sheilsarda/IoT_Thermal_Camera/Lab2/Nikhil Jamdade_A0.pdf

A0 Assignment – ESE516-SPRING 2019 Nikhil Jamdade

Device Description

In developing countries, the patient monitoring systems used in hospitals are not holistically designed compare to the type of monitoring necessary for the patient’s healthcare. The monitoring systems are manual and thus requires time to time check-ups. With increasing number of patients and less availability of resources, hospitals are facing a problem in efficient monitoring system. It is difficult to monitor patient’s health patterns and analyze them. The quality of sleep can be an early indicator of dementia and serious health conditions including adverse reactions to medications, depression and stress. Moreover, some of the vital parameters are really important for early diagnosis of certain medical conditions and understand health status.

The designed IOT device “SmartEye” monitors patient’s sleep, resting pattern, body thermal map and body temperature in real time, in a non-contact way without any wires and devices attached to patients’ body. The system provides patient’s real time temperature, video analysis and thermal analysis. The information from the SmartEye can be accessed and analyzed from the monitoring room or on mobile device application. The ability to track patient’s movement and position non-invasively and monitor them remotely with mobile or desktop applications makes great sense to improve both safety and vigilance. The data received from the product can be analyzed for proper treatment of patient and hospital logistics.

The IOT product SmartEye uses electronic sensors like IR sensor, visible and IR camera module, processing and wireless transmission unit and computational imaging techniques. The patient’s data are acquired using sensor modules and processed using microcontroller (SAMD21). The data is transmitted using WIFI Chip (WINC1500) and internet to personal device or user interface. Though thermal imaging and image analysis is not in widely in practice in medical field before because of only recent development of thermal imaging devices techniques. There is huge scope medical diagnosis by analyzing thermal images and data mining.

Basic Interaction interface of SmartEye

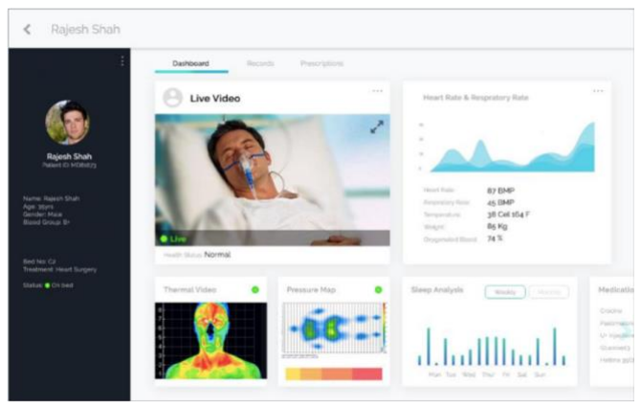
[picture p23: figure]

Simple System Diagram

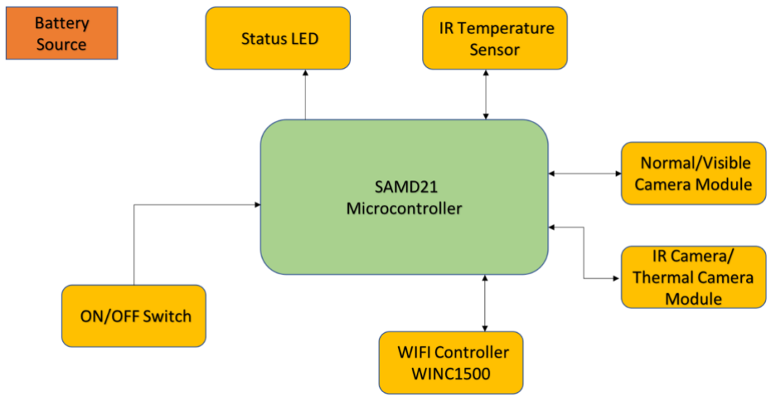
[picture p24: figure]

Device Investigation and Bill of Materials

The excel file having bill of material with its description and links to datasheets is attached with submission.

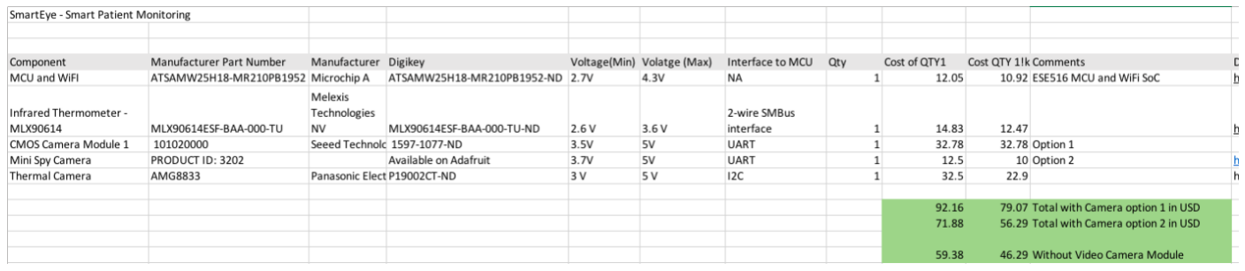
[picture p25: figure]
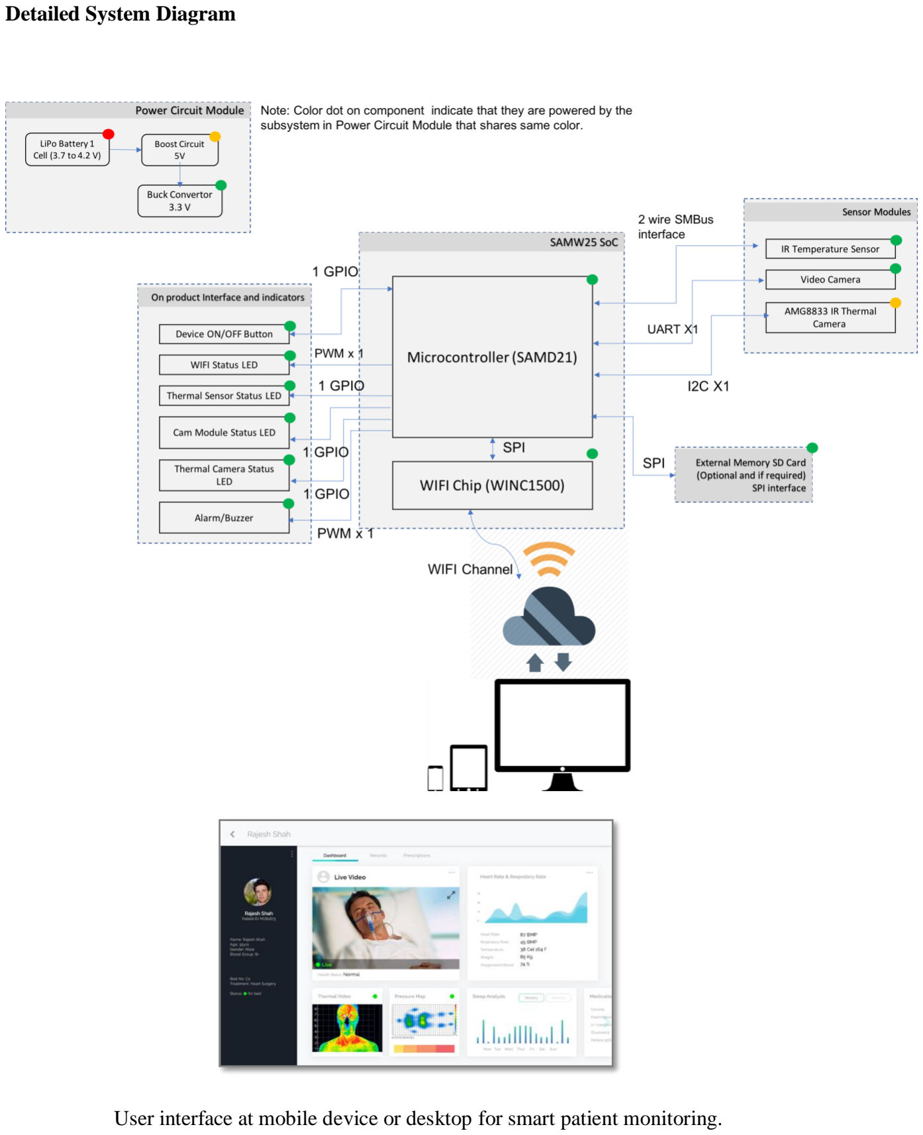
[picture p26: page 3]

Detailed System Diagram

User interface at mobile device or desktop for smart patient monitoring.
