sheilsarda/IoT_Thermal_Camera/Slides/Final_Proj.pdf

# Radiance T

## IOT for Non Contact Temperature Measurement and Thermal Image Mapping

Nikhil Jamdade | Sheil Sarda
Mentor: Eduardo Garcia
ESE 516 IOT Edge Computing | 1st May 2019 | Slide 1/4

## Radiance T – IOT edge Computing

Major Applications -
- Industry 4.0
- Assembly and Manufacturing line
- Smart Retail and Supply Chain
- Consumer and Product Analytics

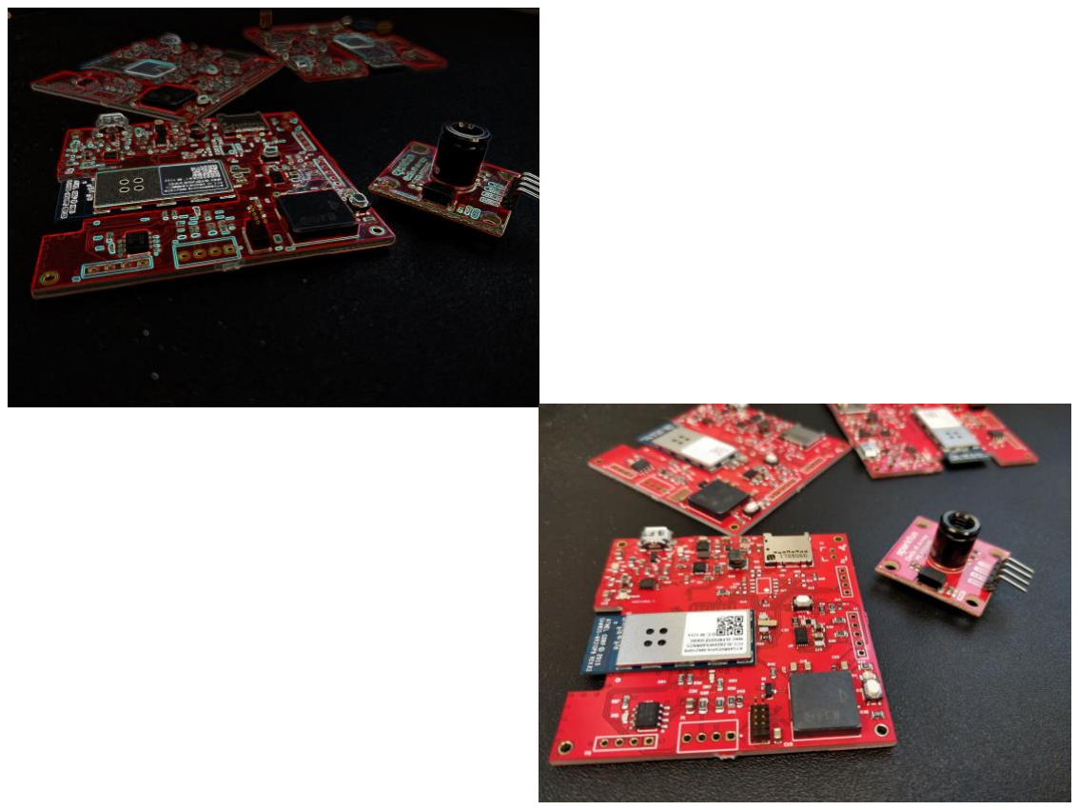
[picture p28: figure]

Device –
1. SAMD 25 WINC 1500
2. IR Sensor and Thermal Camera
3. Fuel Gauge
4. Real Time Update on Cloud Service
5. Analytics Interface

## Roadmap and Challenges

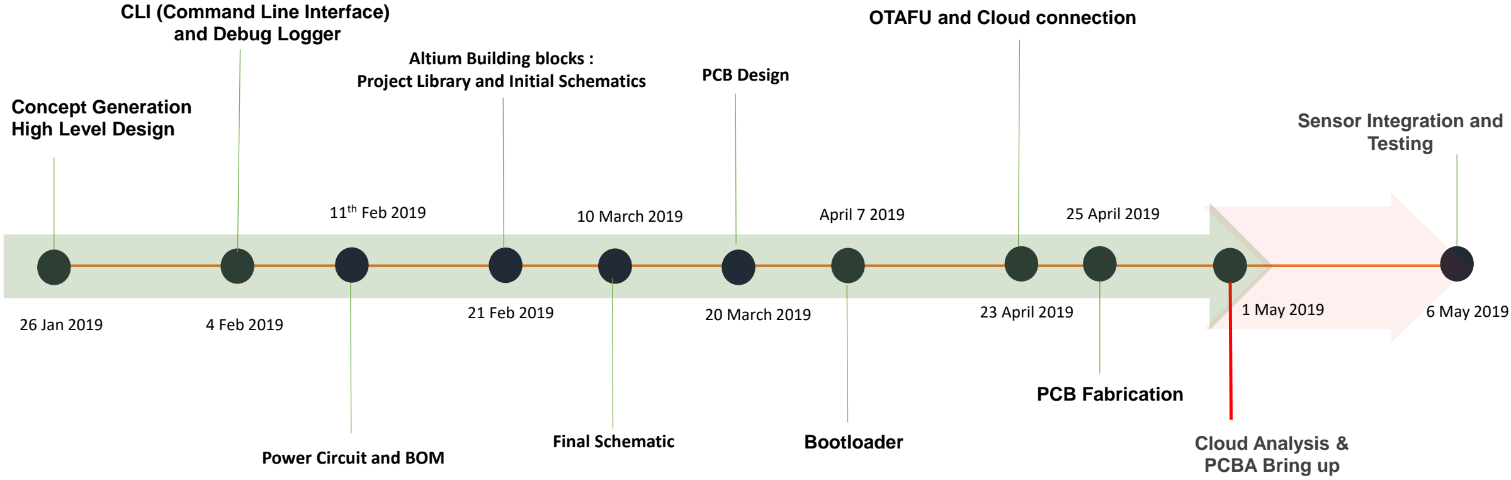
[picture p29: figure]
Concept Generation High Level Design; CLI (Command Line Interface) and Debug Logger; PCB Fabrication; OTAFU and Cloud connection; 26 Jan 2019; 4 Feb 2019; 21 Feb 2019; 20 March 2019; 23 April 2019; Bootloader; Cloud Analysis &; PCBA Bring up; Sensor Integration and Testing; Power Circuit and BOM; Altium Building blocks :; Project Library and Initial Schematics; PCB Design; 25 April 2019; 1 May 2019; 6 May 2019; April 7 2019 th Feb 2019; Final Schematic; 10 March 2019

## Interacting with Radiance T

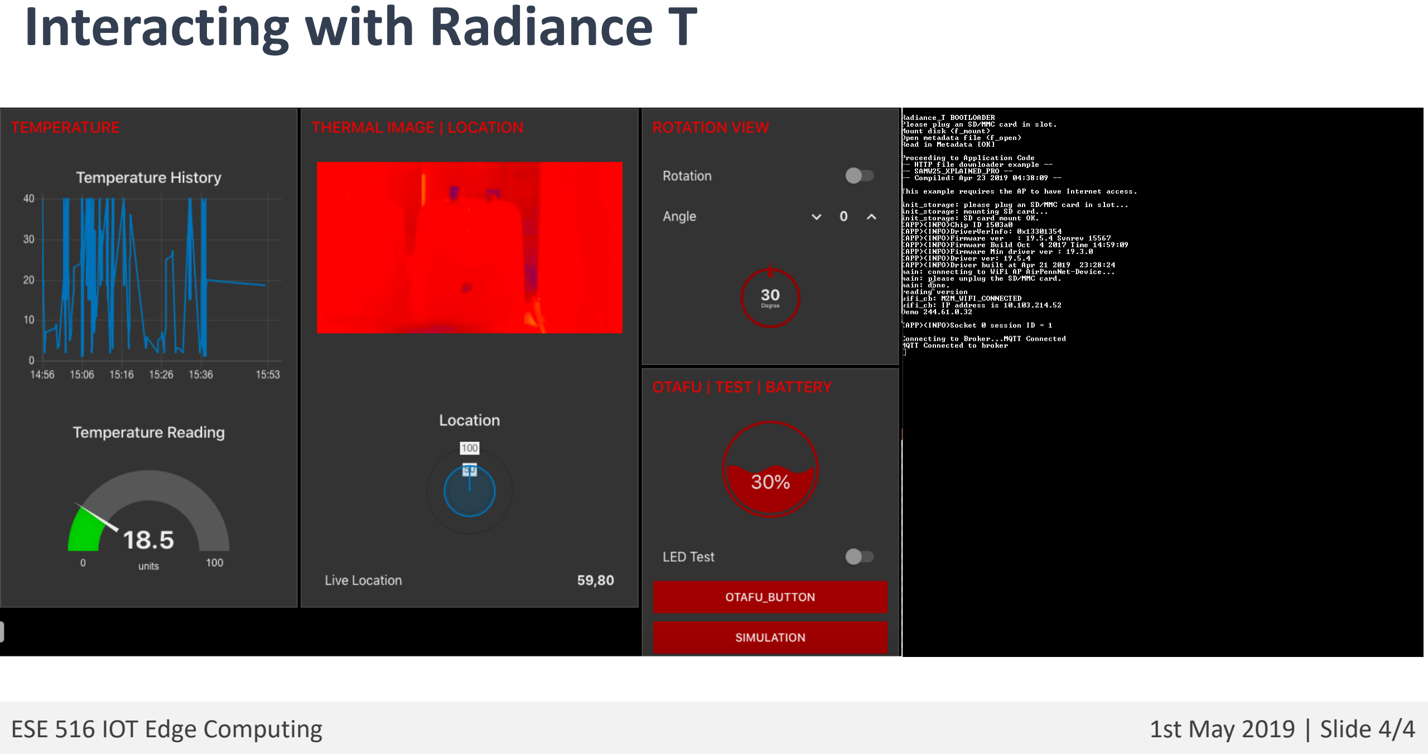
[picture p30: page 4]
