sheilsarda/IoT_Thermal_Camera/Lab7/A7 Submission/Q1_Node_Red/Flow Diagram.pdf

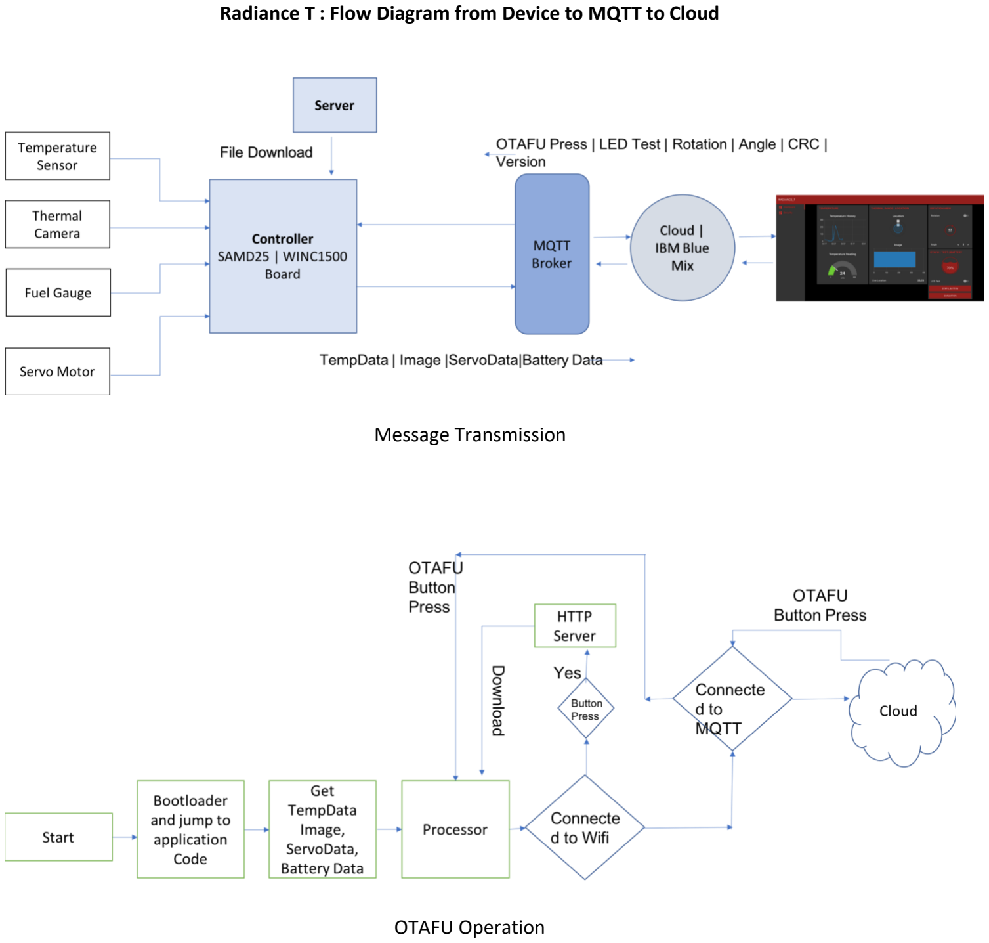
[picture p136: page 1]

Radiance T : Flow Diagram from Device to MQTT to Cloud

Message Transmission

OTAFU Operation

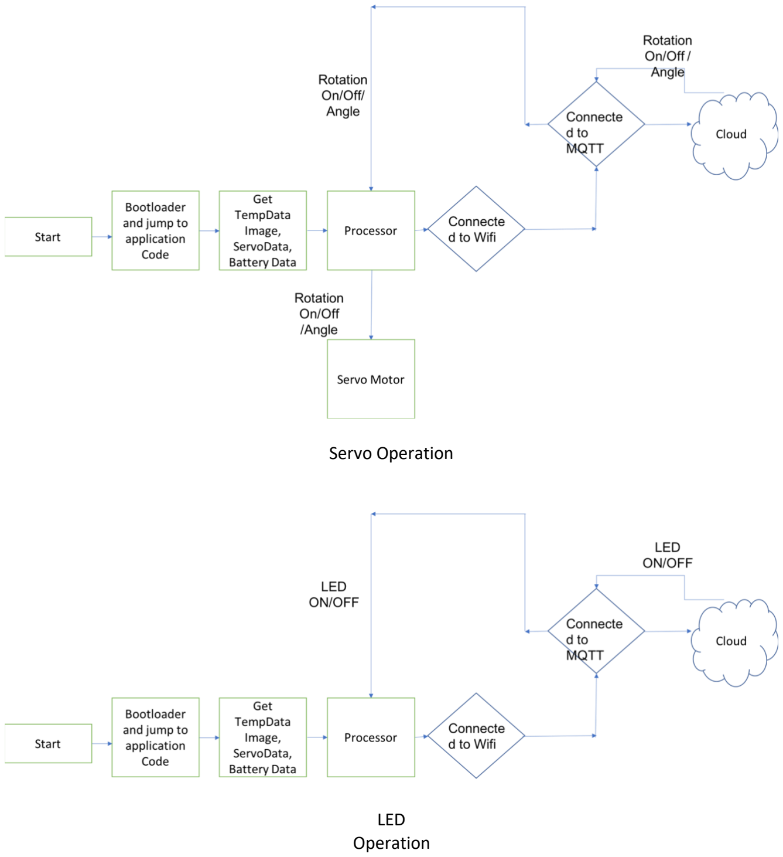
[picture p137: page 2]

Servo Operation

LED
Operation

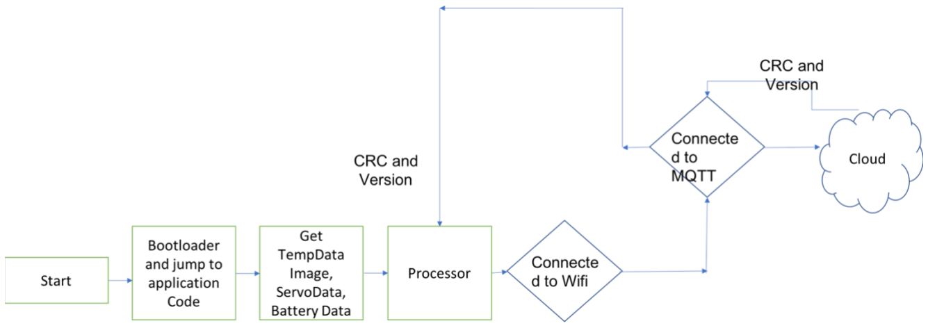
[picture p138: figure]

MetaData Trasfer
