sheilsarda/IoT_Thermal_Camera/Lab7/A7 Submission/Q1_Node_Red/Radiance T_Node Red Simulator .pdf

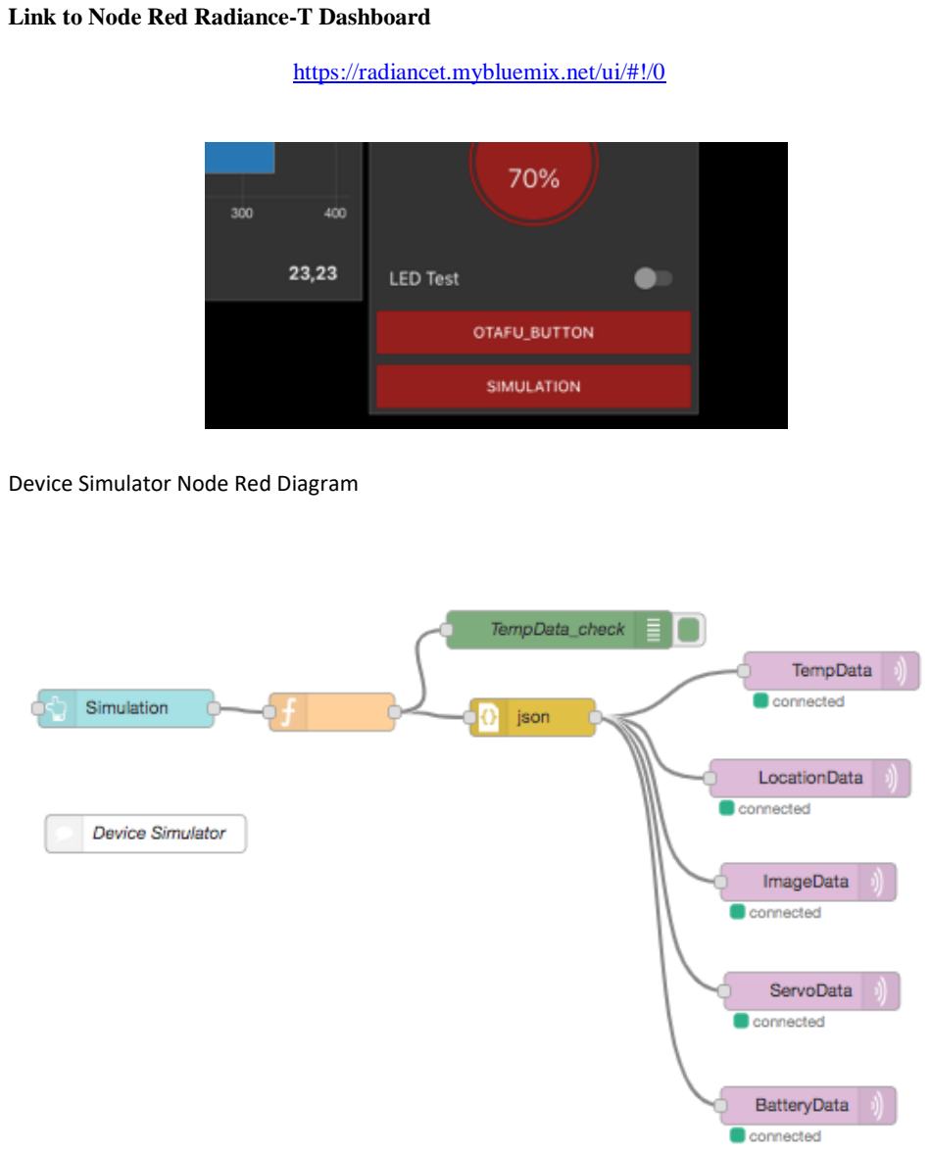
[picture p139: page 1]

Link to Node Red Radiance-T Dashboard

https://radiancet.mybluemix.net/ui/#!/0

Device Simulator Node Red Diagram
