sheilsarda/IoT_Thermal_Camera/Lab1/ESE516 A1.pdf

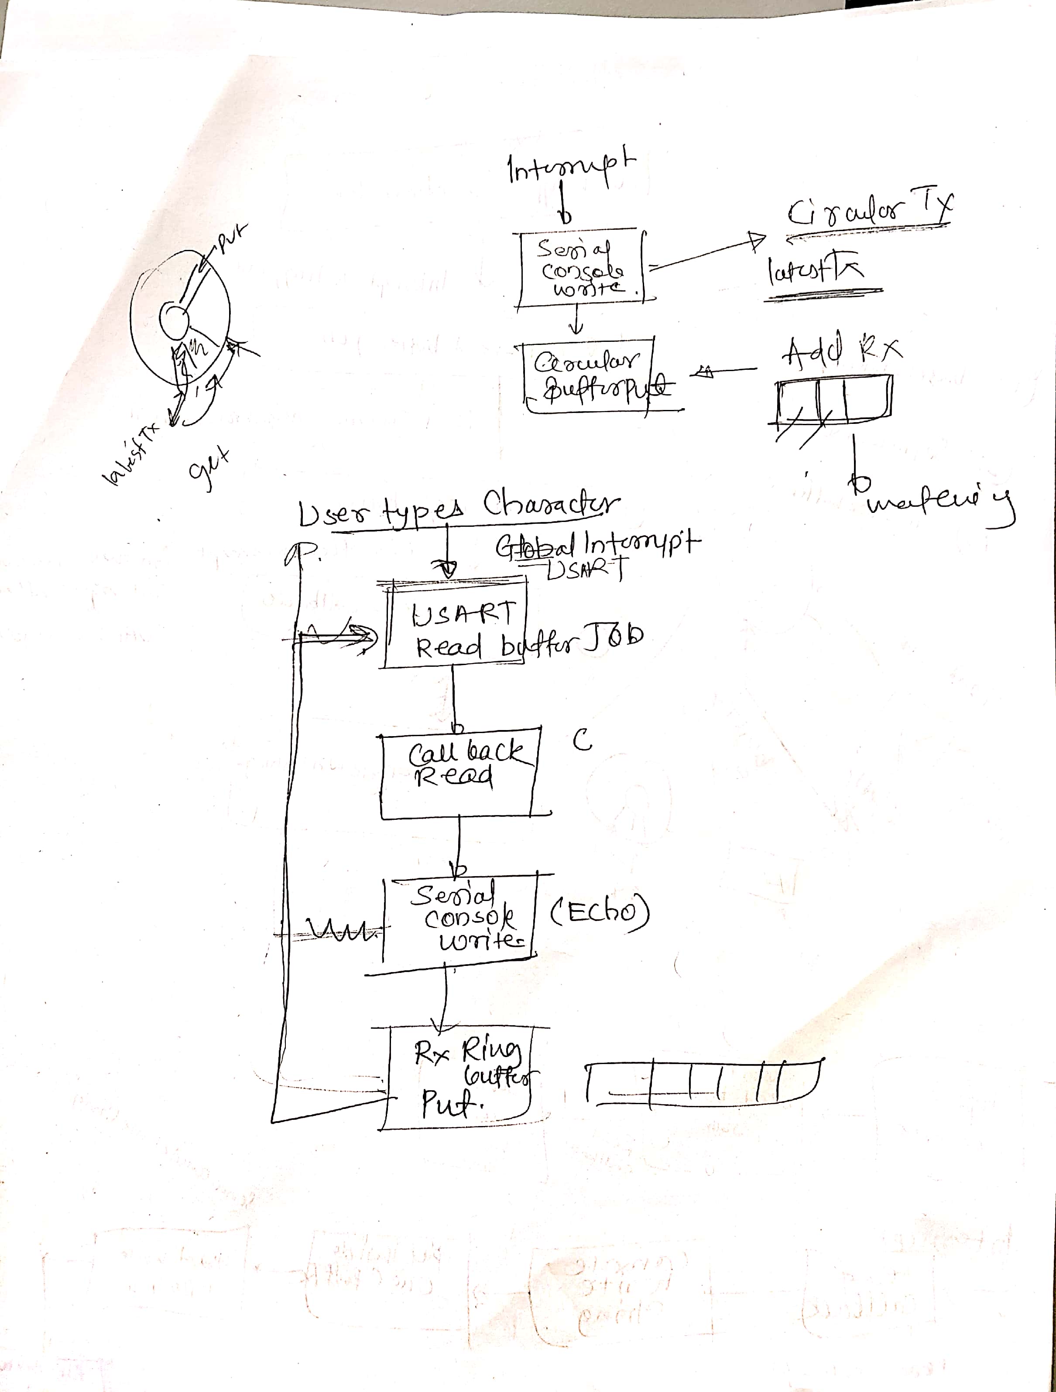
[picture p149: page 1]

Scanned by CamScanner

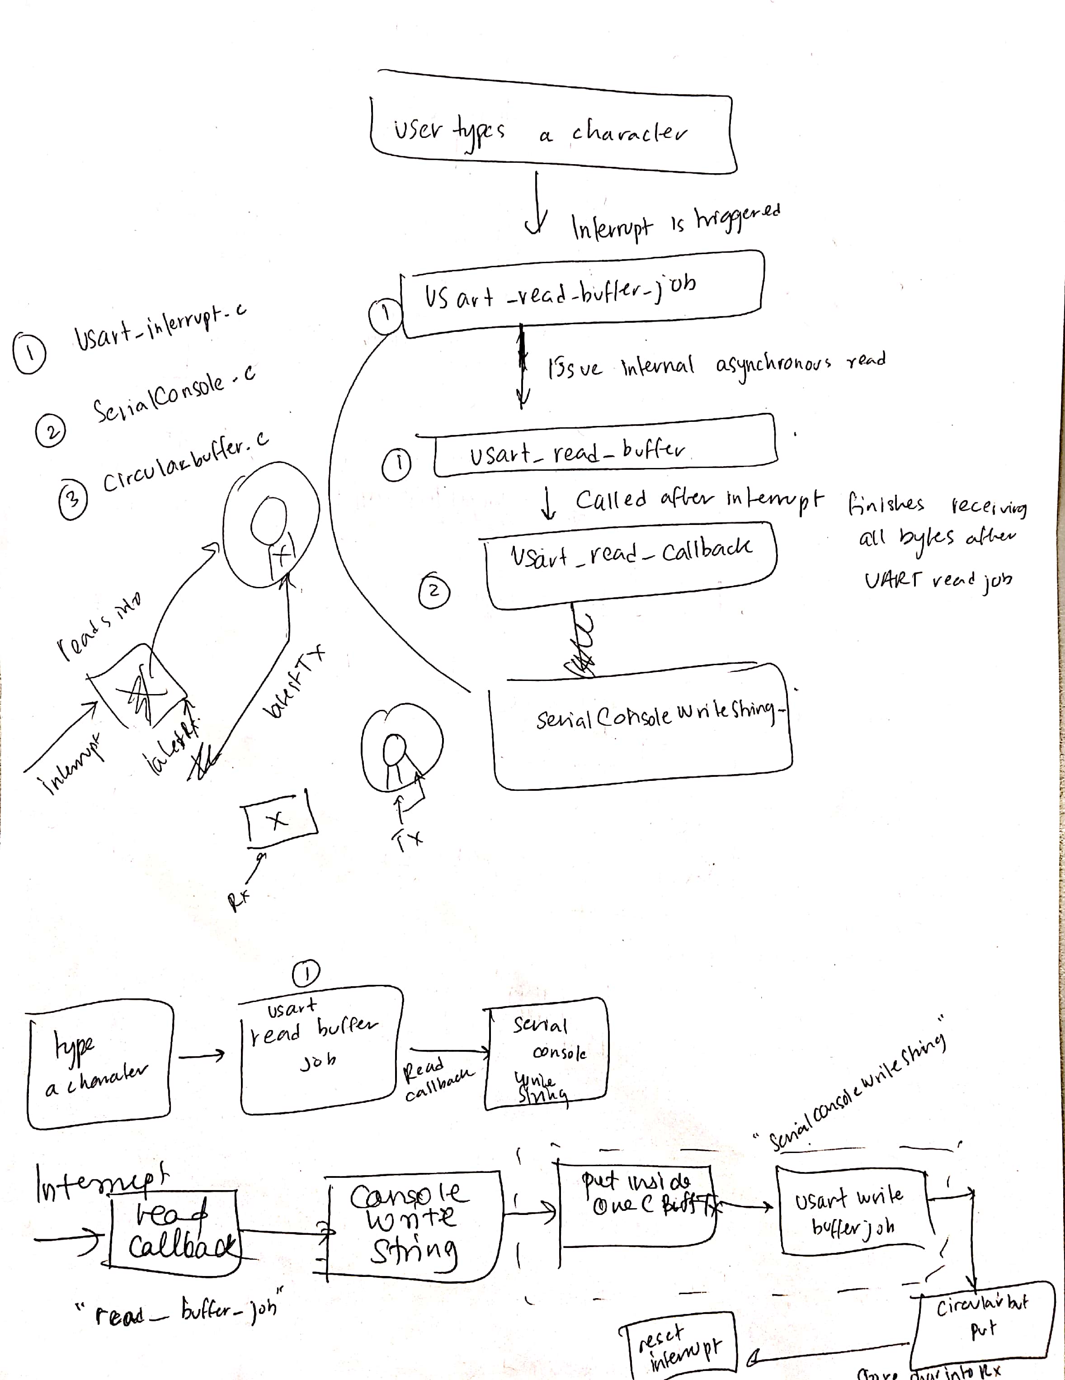
[picture p150: page 2]
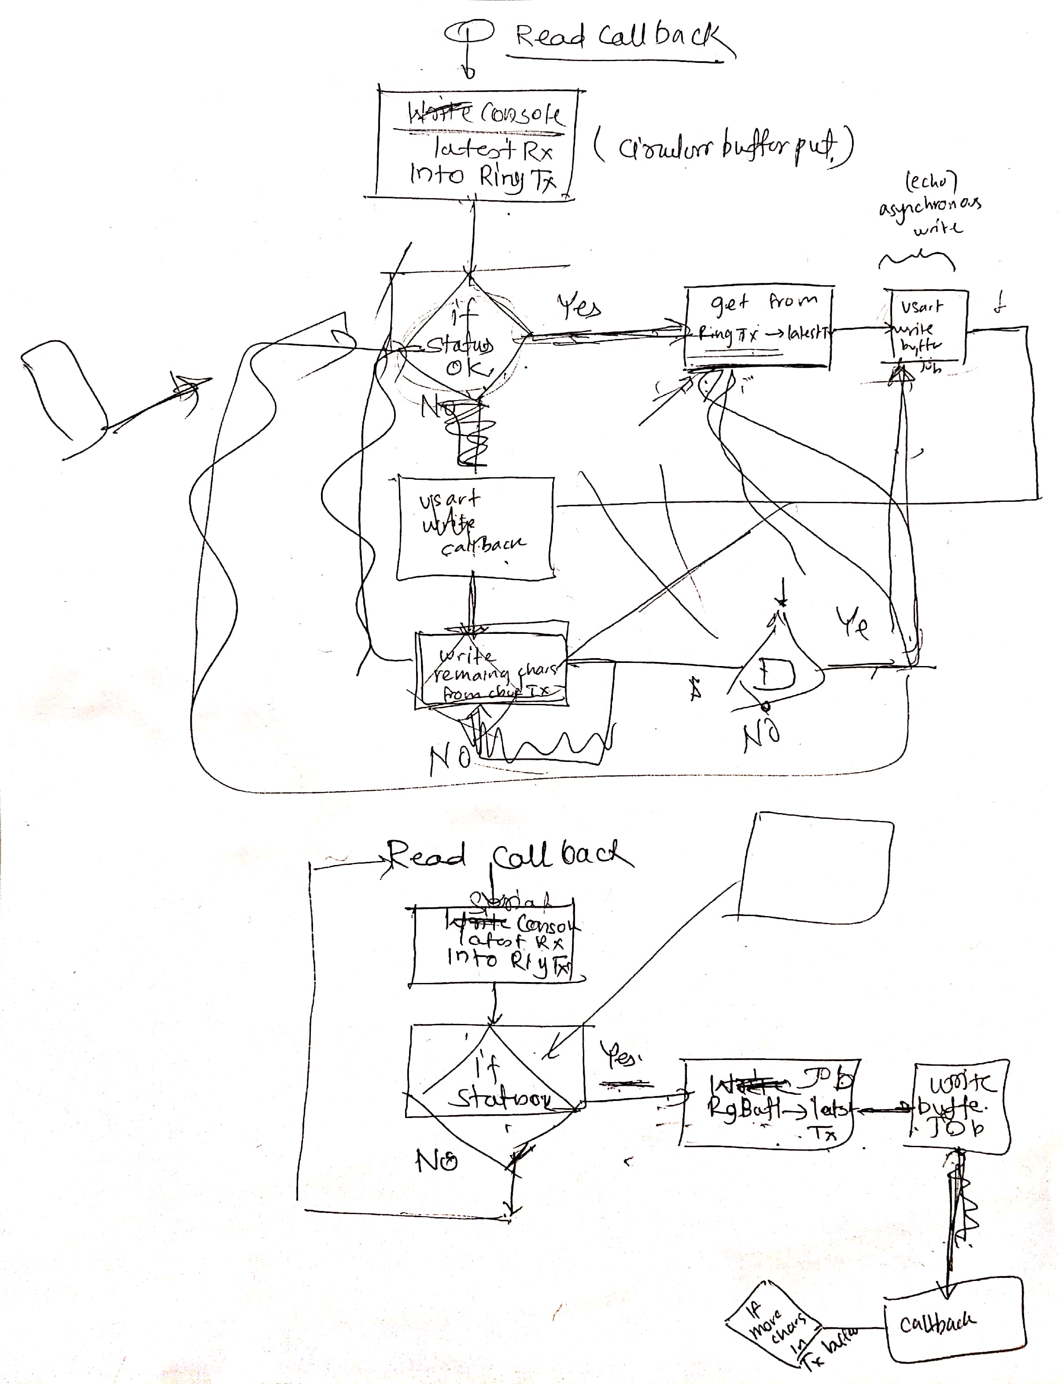
[picture p151: page 3]
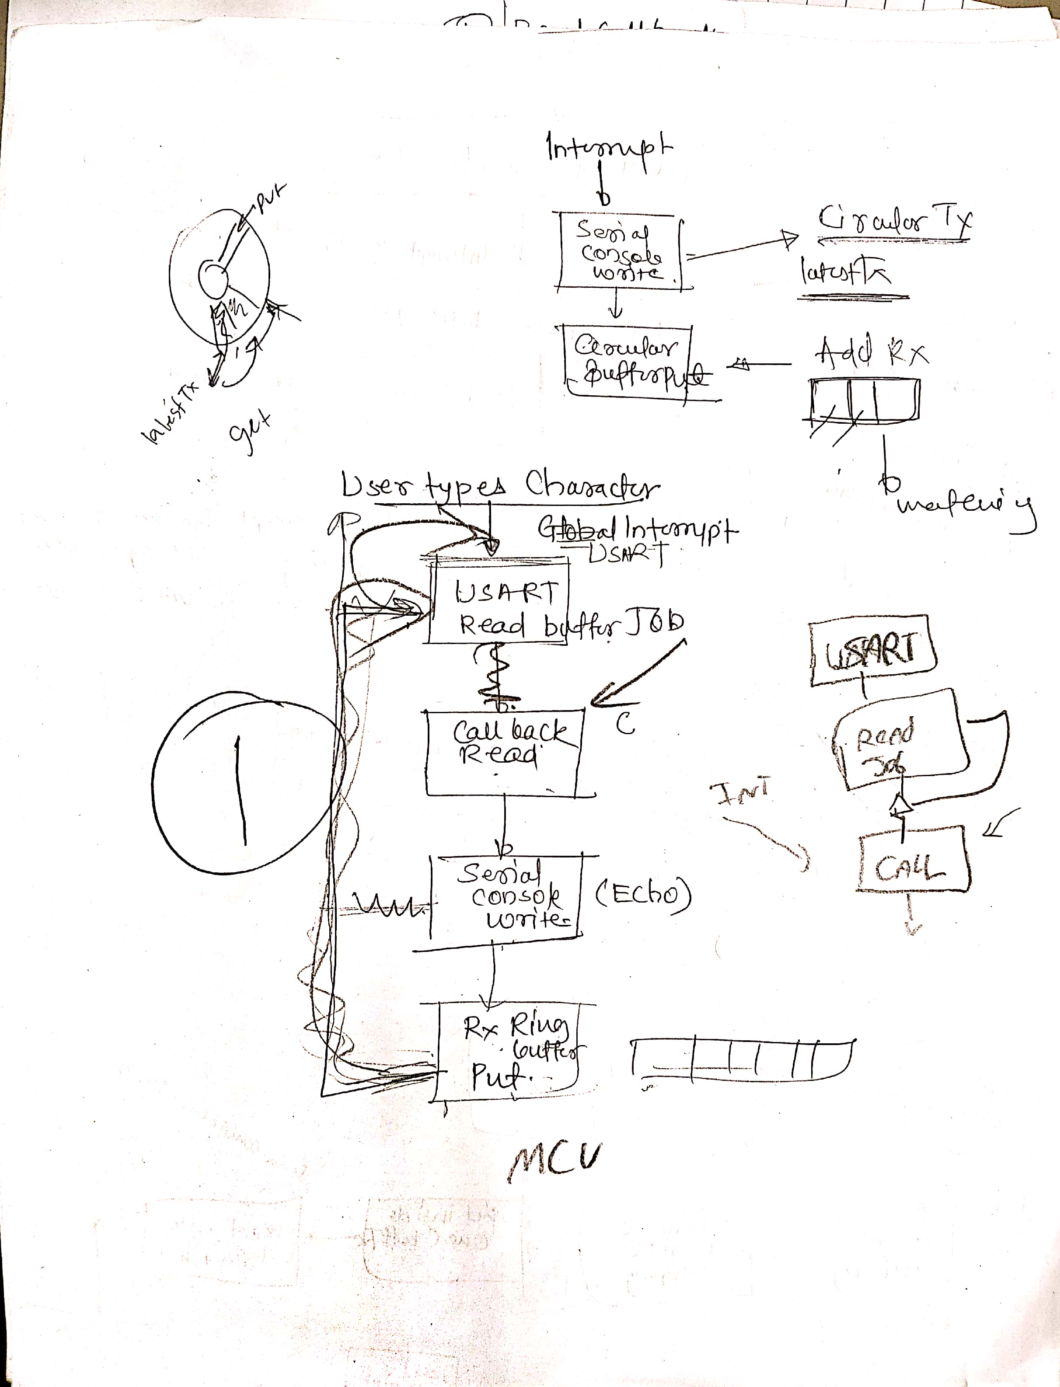
[picture p152: page 4]
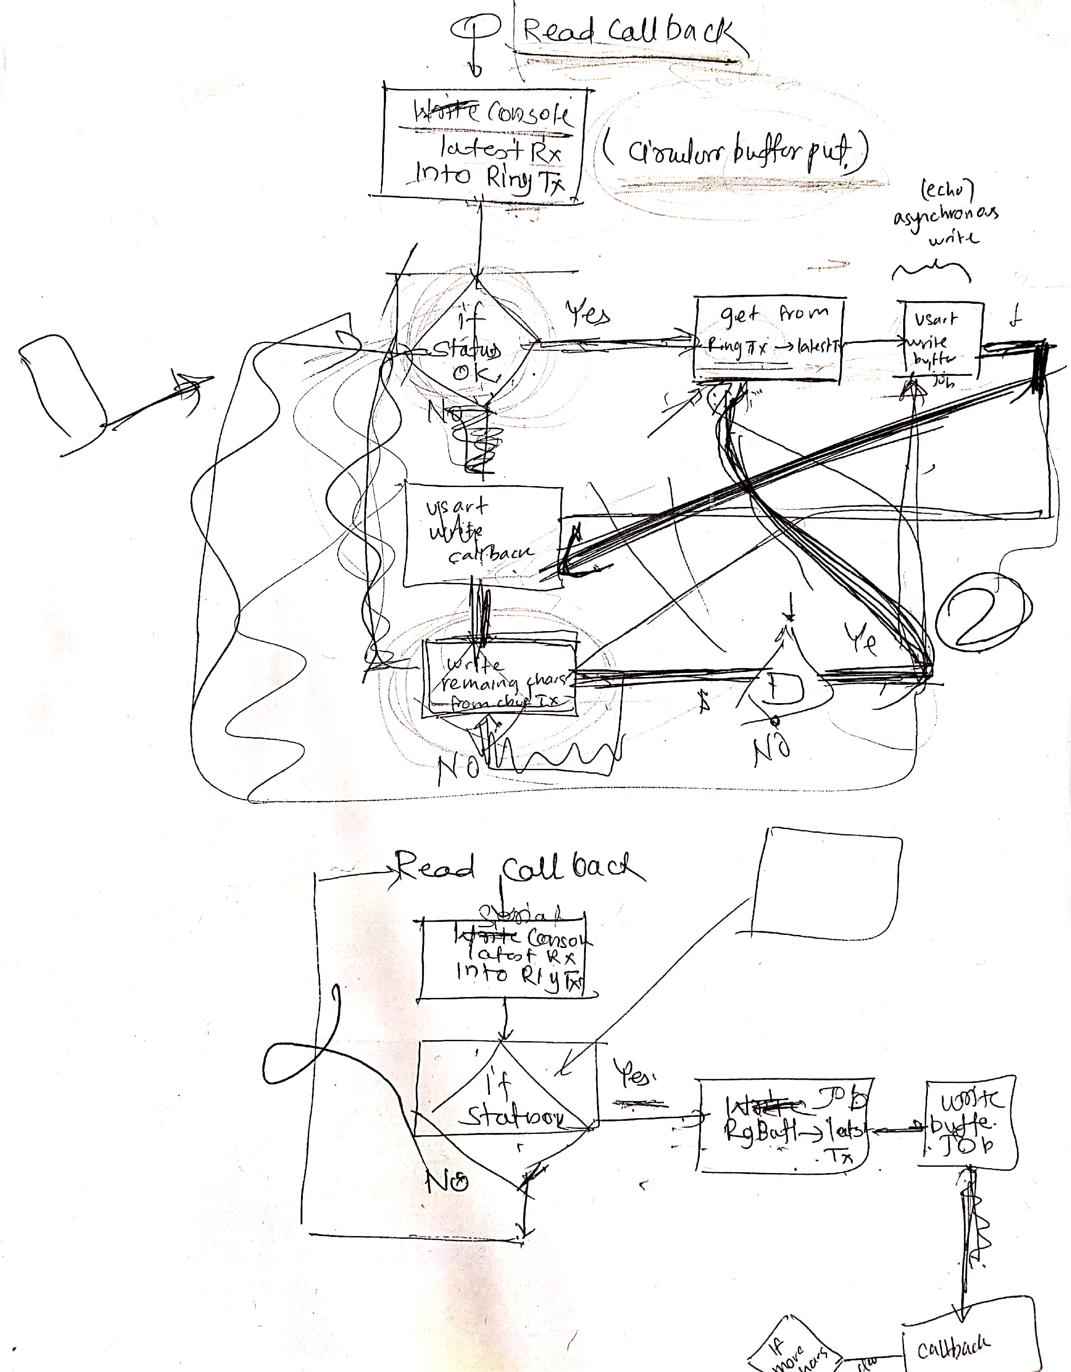
[picture p153: page 5]
