sheilsarda/IoT_Thermal_Camera/Slides/Lecture16_ESE516_2019-1.pdf

# L16: FLASH LAB

ESE516: IoT Edge Computing Wednesday March 28 2019
Eduardo Garcia – edgarc@seas.upenn.edu

## RASPBERRY PI(DAY) ZERO W ANTENNA

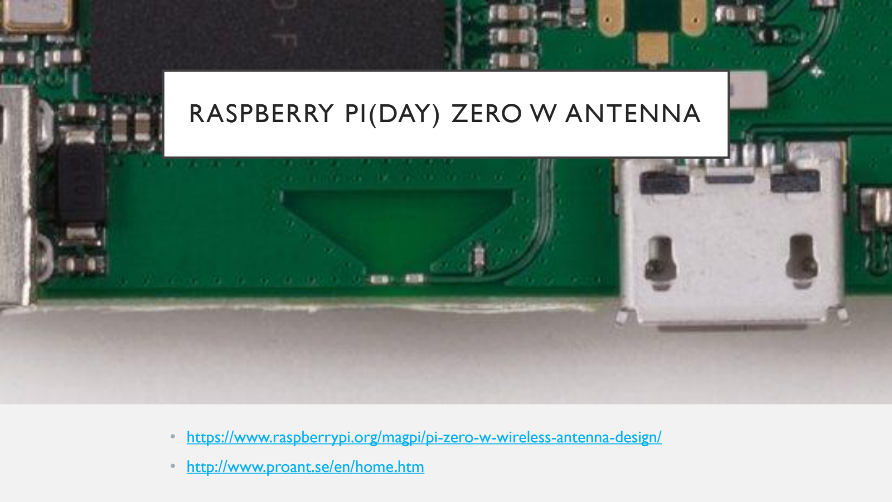
[picture p154: page 2]

- https://www.raspberrypi.org/magpi/pi-zero-w-wireless-antenna-design/
- http://www.proant.se/en/home.htm

## TODAY’S LAB GOALS

1. Atmel Studio Solution
1. Create 2-project solution, including bootloader + app code
2. Modify the linker and program erasure settings
2. Flash
1. Connect to your Flash IC using the ASF driver.
2. Read in the Flash ID to validate the connection.
3. Read a memory location in flash.
4. Erase a memory location in flash.
5. Write a memory location in flash.

## BONUS GOALS

If you happen to get through all of the flash…

1. Import and test the ASF CRC32 driver.
1. Try running the checksums on a bunch of generated data, writing it to flash, reading it back out, and validating it.
2. http://asf.atmel.com/docs/3.34.1/samd21/html/group__common__services__crc32.html
2. Import and test the ASF NVM driver.
1. This writes to the SAM D21 non volatile memory. It’s what we’re going to use to write the application code to memory, while in the bootloader.
2. http://asf.atmel.com/docs/3.34.1/samd21/html/group__asfdoc__sam0__nvm__group.html

# BOOTLOADER REVIEW

## PARTITION TABLES

- Remember the caveats of your flash memory!
- How small of a chunk of memory can you erase?
- How many bytes can you write at a time?
- You must erase before writing to a section of memory.
- What do you want to store in your status page?

External
Flash
SD CARD
FILE 1 | BinaryUpdate
FILE2 | BINARY metadata
FILE 3 | Other Data
SAMD21 256kB | 0x00000 | Bootloader
| 0x01F00 | Boot status
| 0x02000 | Application Code
| 0x40000 | End of memory

## STATUS STRUCTURE

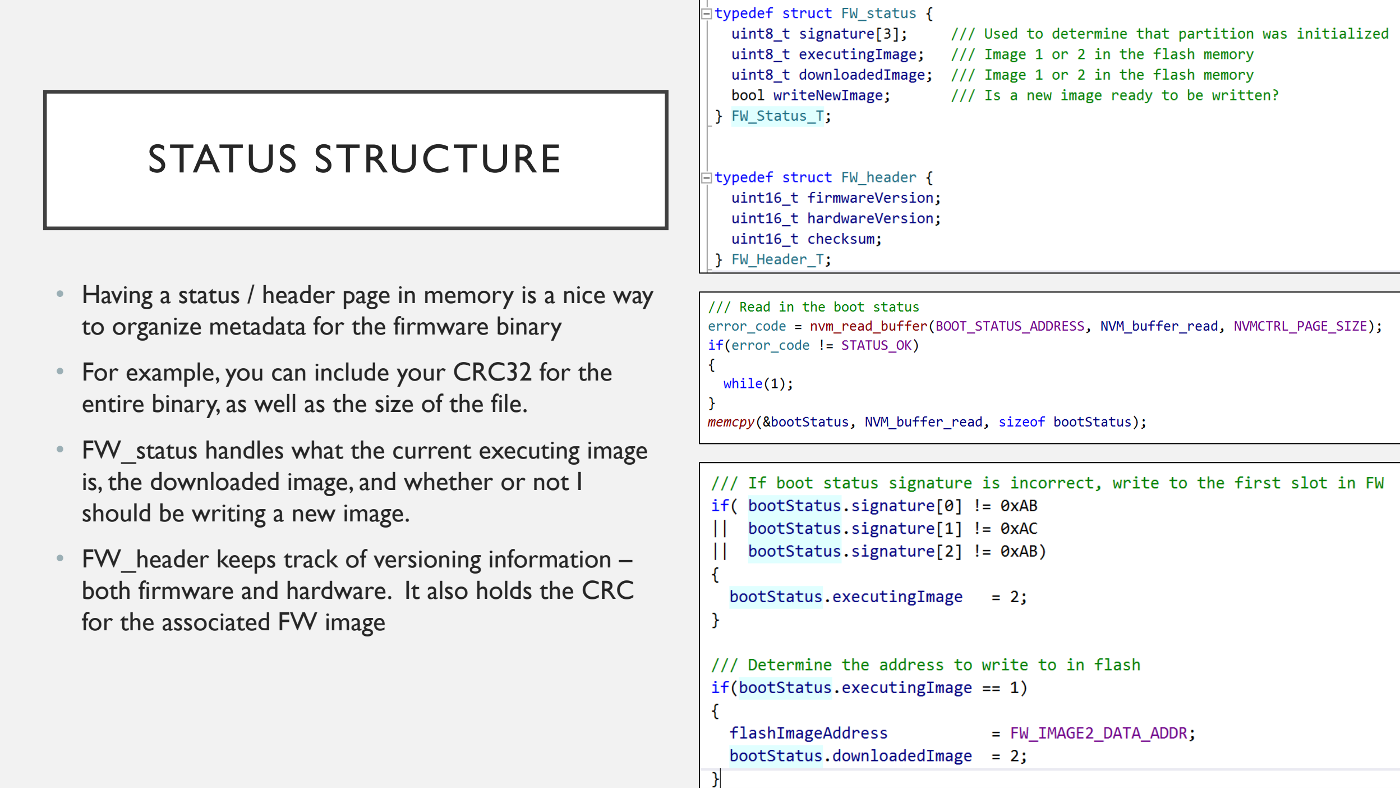
[picture p155: page 9]

- Having a status / header page in memory is a nice way to organize metadata for the firmware binary
- For example, you can include your CRC32 for the entire binary, as well as the size of the file.
- FW_status handles what the current executing image is, the downloaded image, and whether or not I should be writing a new image.
- FW_header keeps track of versioning information – both firmware and hardware. It also holds the CRC for the associated FW image

## RUNNING APPLICATION CODE

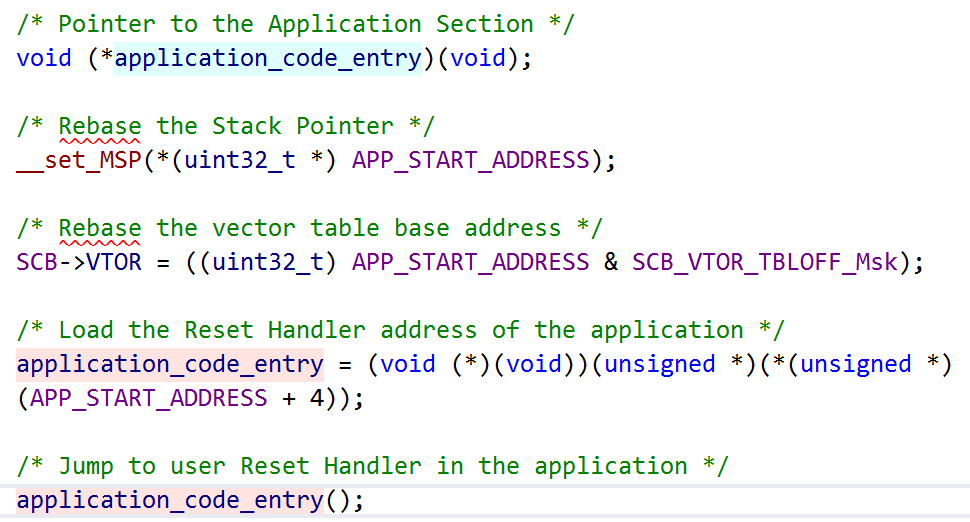
[picture p156: figure]

- On boot, the MCU will look to the 0x0000 address – this gives the stack pointer and reset handler for the bootloader
- To transition to the application code, we must point to the application code space – “rebase” the stack pointer & reset vector
- The code on the right handles this functionality
- USB MSC: Page 31-32 has some good references
- http://www.atmel.com/images/atmel-42352-sam-d21-xpro-usb-host-msc-bootloader_trainingmanual_an8185.pdf (http://www.atmel.com/images/atmel-42352-sam-d21-xpro-usb-host-msc-bootloader_training-manual_an8185.pdf)

# ATMEL STUDIO SOLUTION

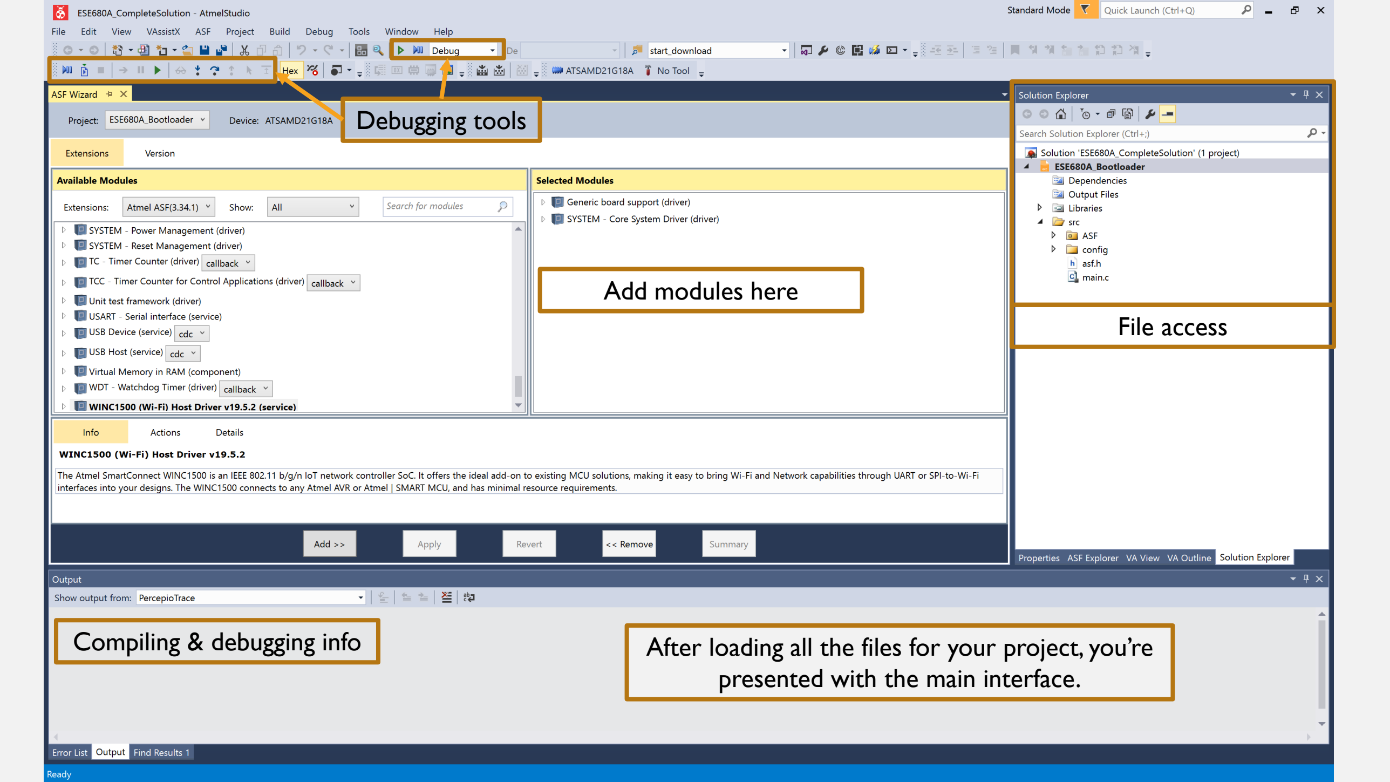
[picture p157: page 12]

File access

Compiling & debugging info

Add modules here

Debugging tools

After loading all the files for your project, you’re presented with the main interface.

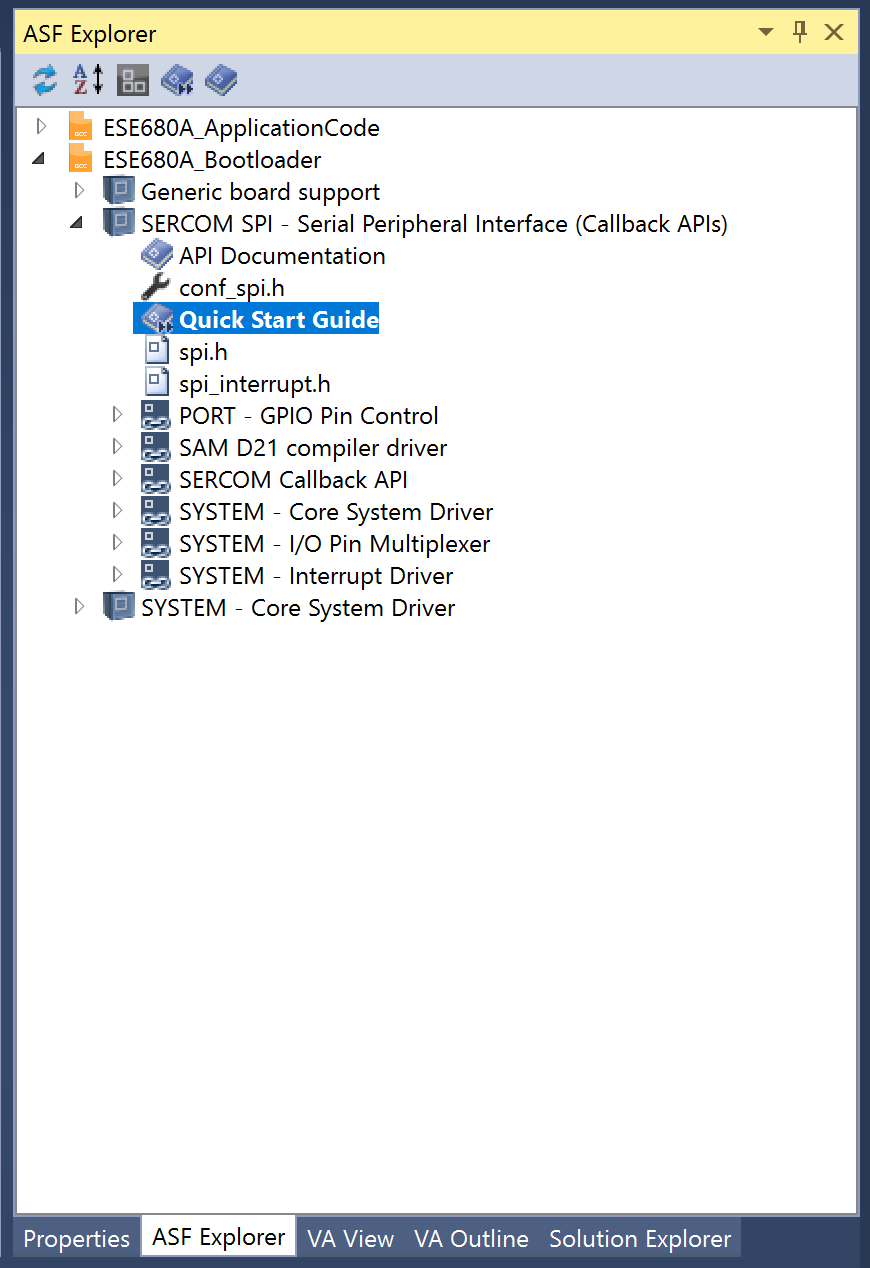
[picture p158: figure]

## FINDING INFO ON MODULES / DRIVERS

- Atmel has a fair amount of documentation for their drivers.
- In the ASF Explorer panel, you can find:
- API Documentation: Descriptions of all functions and variables
- Quick Start Guides (usually): Configuration information and explanations on how to use the code.

# CREATE A 2-PROJECT SOLUTION

## SOLUTIONS &

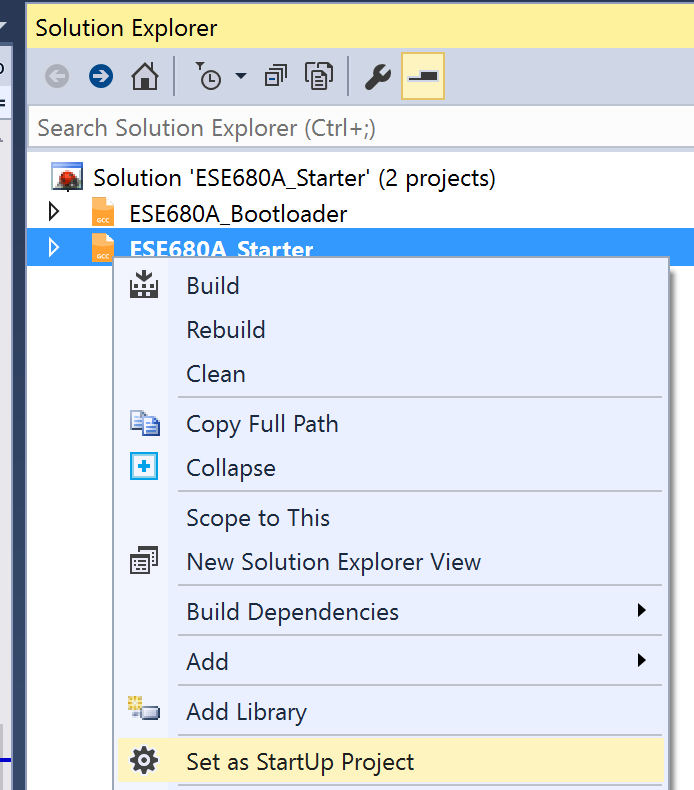
[picture p159: figure]

## PROJECTS

- A project contains multiple source files that compile to a single, flashable binary
- A solution is a collection of related projects – a workspace.
- You may only target one project for compiling and debugging at a time: Set as StartUp Project

Project #1:
bootloader

Project #2:
application_code

Solution: ese516

## BOOTLOADER PROJECT

- You’ll want two projects in your solution.
- One for the bootloader
- One for the application code
- Start Atmel Studio up, and don’t have anything else open.

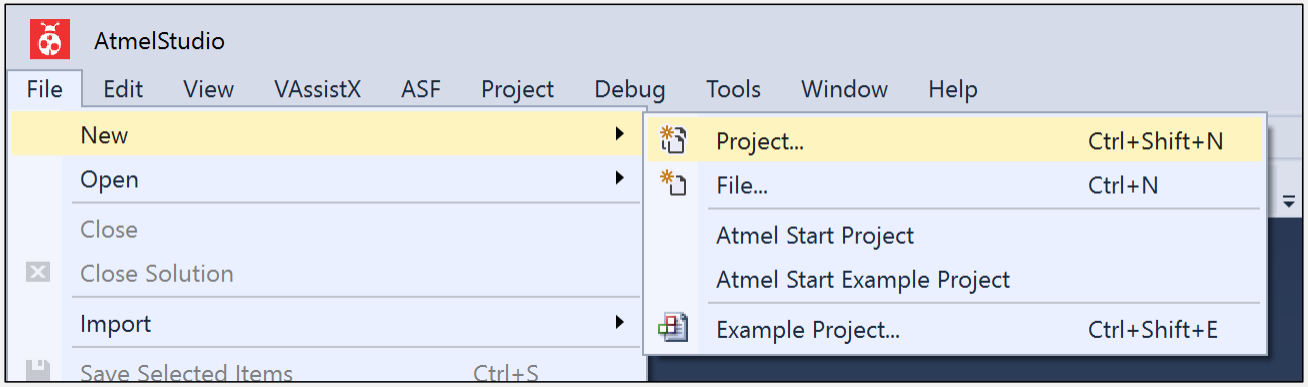
[picture p160: figure]
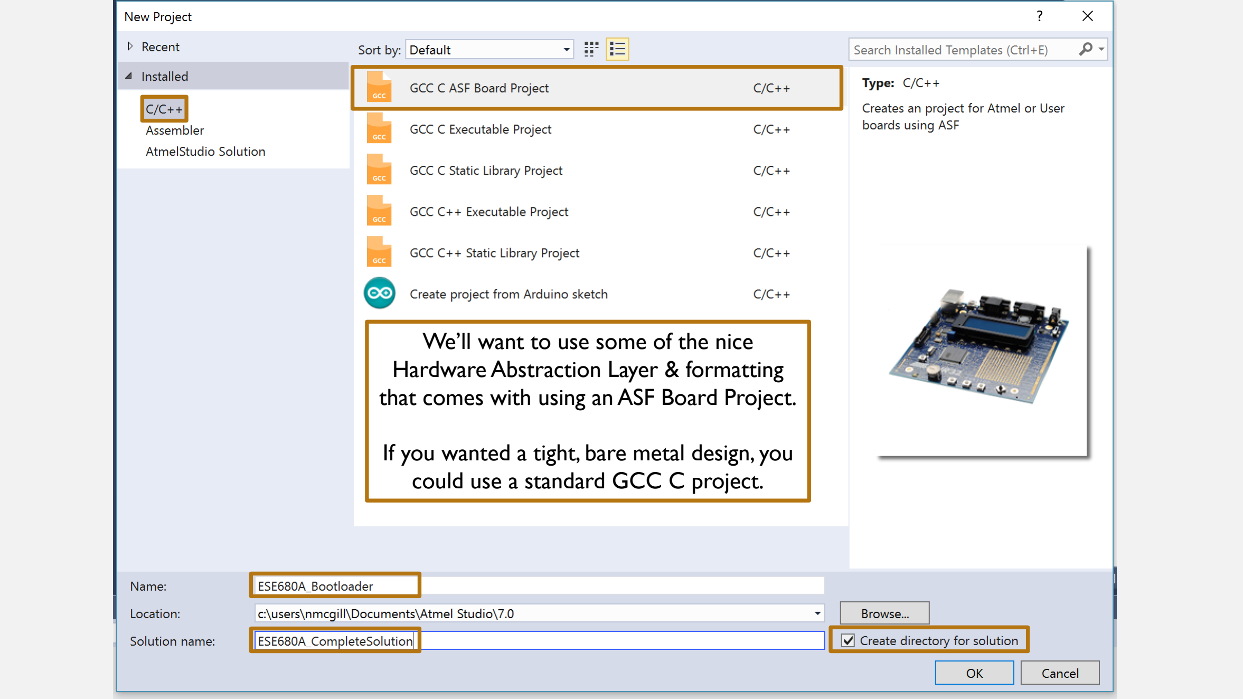
[picture p161: page 17]

We’ll want to use some of the nice Hardware Abstraction Layer & formatting that comes with using an ASF Board Project.

If you wanted a tight, bare metal design, you could use a standard GCC C project.

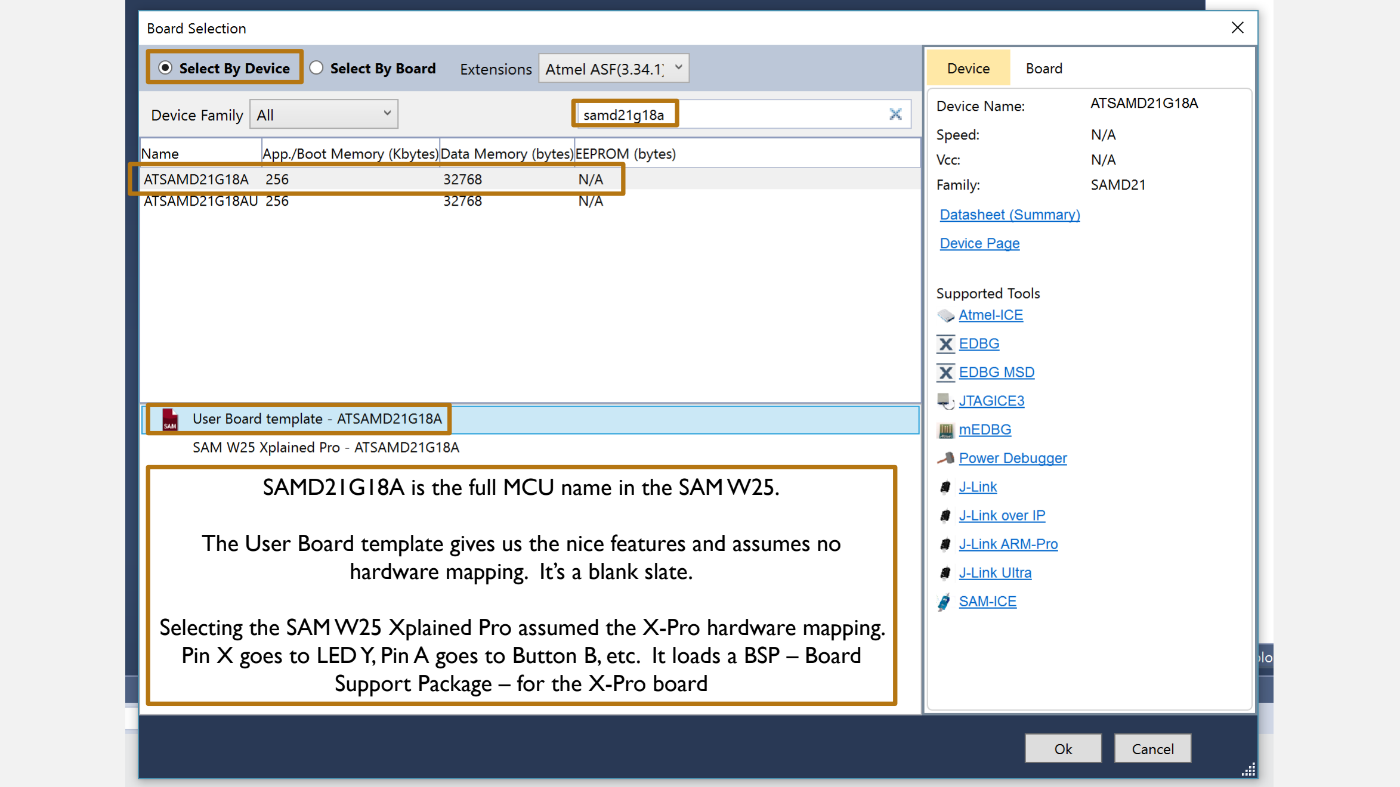
[picture p162: page 18]

SAMD21G18A is the full MCU name in the SAM W25.

The User Board template gives us the nice features and assumes no hardware mapping. It’s a blank slate.

Selecting the SAM W25 Xplained Pro assumed the X-Pro hardware mapping. Pin X goes to LED Y, Pin A goes to Button B, etc. It loads a BSP – Board Support Package – for the X-Pro board

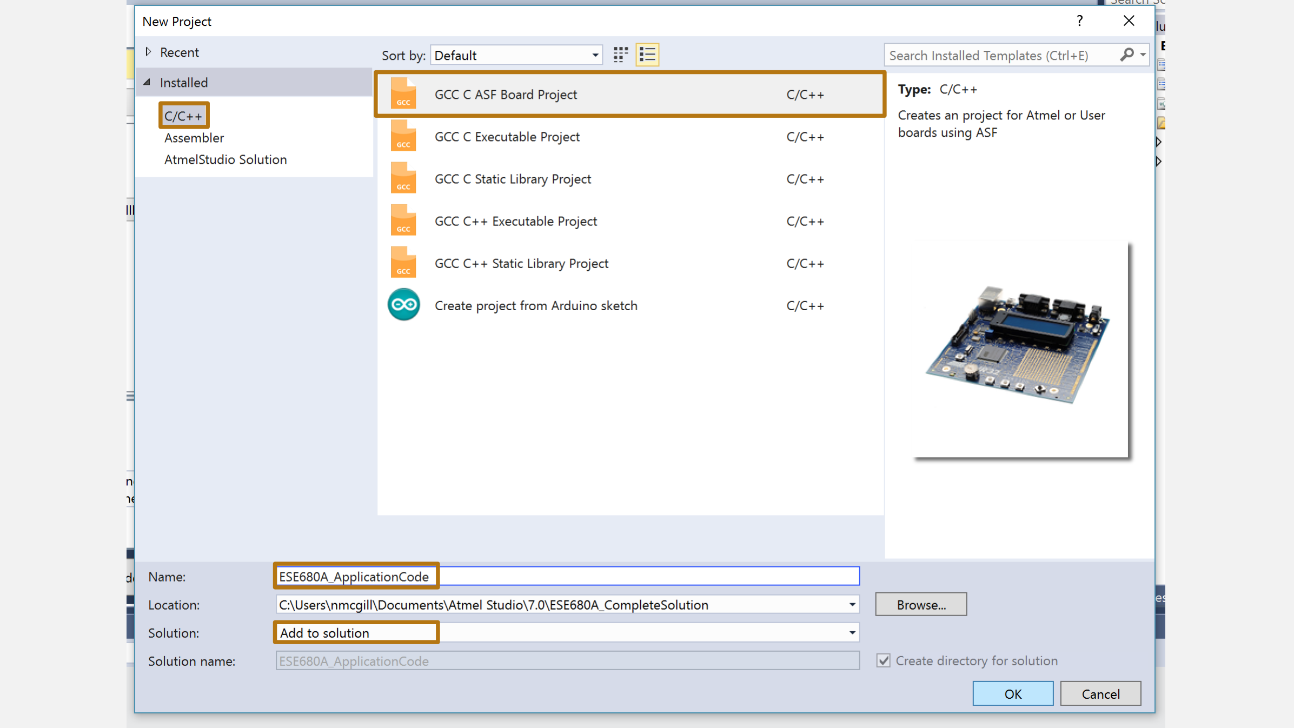
[picture p163: page 19]

## SPECIFYING A PROJECT IN A MULTI-PROJECT SOLUTION

- Once you have more than one project in a solution, Atmel Studio’s compiling / debugging controls will only load one project at a time.
- How do you switch between the two?
- Find the Solution Explorer panel.
- Right-click the desired project, and click Set as StartUp Project
- Debug away!

# PROJECT SETTINGS

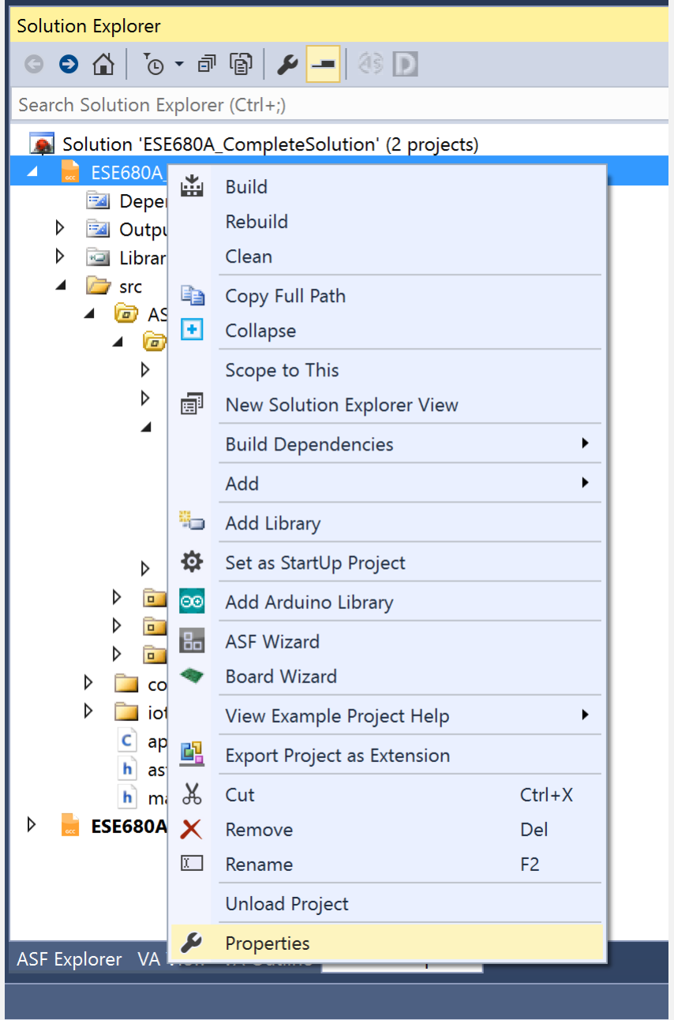
[picture p164: figure]

## PROJECT PROPERTIES

- Project Properties includes:
- Build settings (optimizations)
- Debugging tool support
- Pre & post build events (do you want to run scripts? Build in an SVN revision number?)

## BOOTLOADER CODE: SET PROGRAM ERASURE

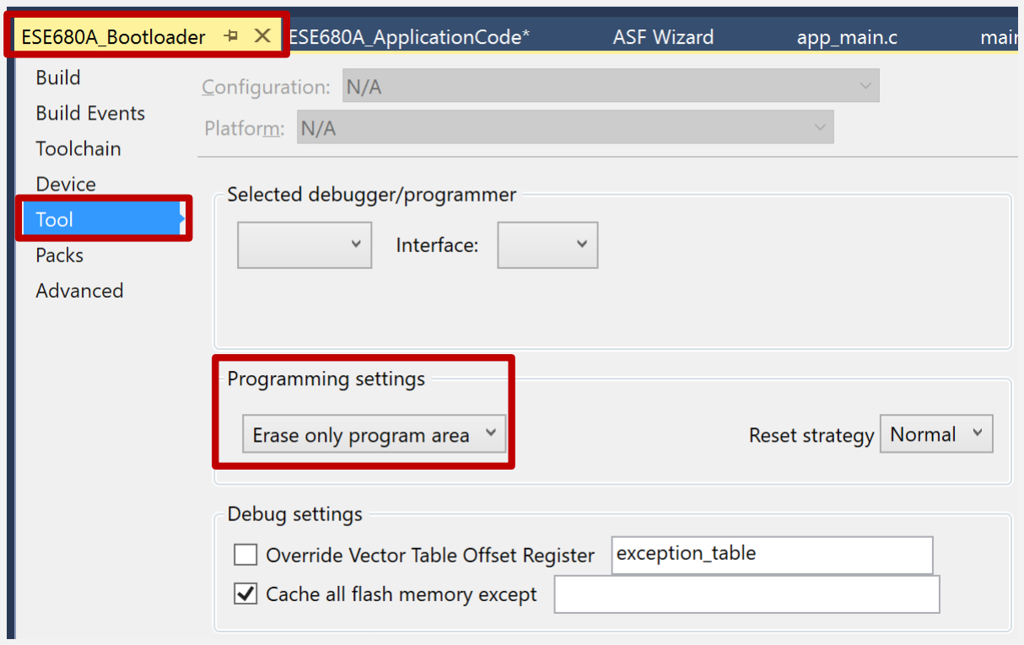
[picture p165: figure]

- If we want to load the bootloader and application code from Atmel Studio, we want to make sure we’re not erasing the wrong parts of code.
- You may want to do differently, but you can set the Programming settings to only erase the program area for the bootloader.
- This way, you can update your bootloader code without erasing your app code.
- In Project Properties, find the Tool pane on the left hand side to set this.

## APP CODE: SET

## PROGRAM ERASURE

- Same thing as the bootloader. When you load your app code, you don’t want to erase the bootloader each time.
- In Project Properties, find the Tool pane on the left hand side to set this.

## APP CODE: SET LINKER OFFSET

- Our application code will not live at 0x0000, the default address. It will be living at 0x2000 into memory.
- We need to set this appropriately in our compiling settings so the code knows where it lives. This is handled by the linker offset.
- You can find it in Toolchain > Miscellaneous > Linker Flags
- Add “ -Wl,--section-start=.text=0x2000” to the end of your linker flags. Mine looks like:
- -Wl,--entry=Reset_Handler -Wl,--cref -mthumb -T../src/ASF/sam0/utils/linker_scripts/samd21/gcc/samd21g18a_flash.ld -Wl,--section-start=.text=0x2000
- Learn more about Linkers: https://www.microchip.com/webdoc/GUID-ECD8A826-B1DA-44FC-BE0B-5A53418A47BD/index.html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 (https://www.microchip.com/webdoc/GUID-ECD8A826-B1DA-44FC-BE0B-5A53418A47BD/index.html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)

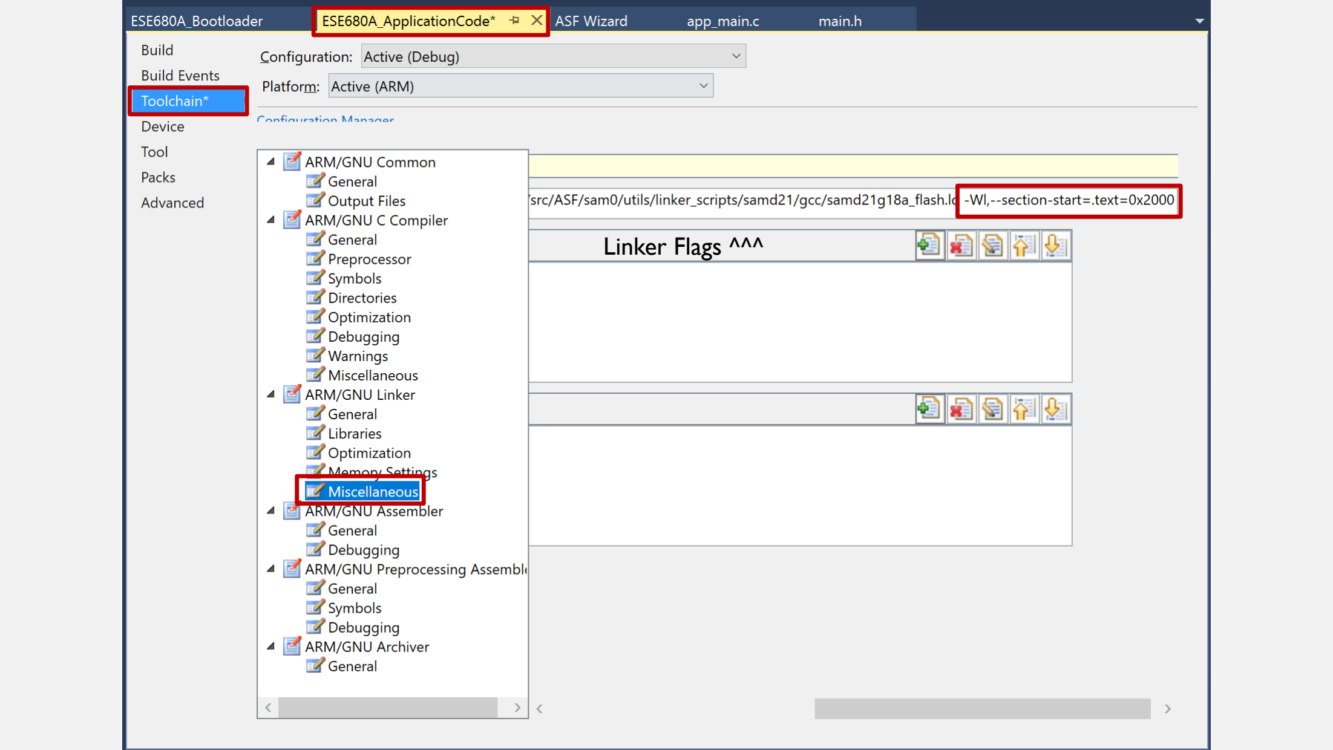
[picture p166: page 26]

Linker Flags ^^^

# TIPS

## NVM ASF DRIVER

- ASF has a driver (NVM) that has an API to write to the MCU’s flash.
- Try the example! It does reads and write – (http://asf.atmel.com/docs/latest/samd21/html/asfdoc_sam0_nvm_basic_use_case.html) just what you need right? http://asf.atmel.com/docs/latest/samd21/html/asfdoc_sam0_nvm_basic_use_case. html (http://asf.atmel.com/docs/latest/samd21/html/asfdoc_sam0_nvm_basic_use_case.html)
- Read the documentation!
http://asf.atmel.com/docs/latest/samd21/html/group__asfdoc__sam0__nvm__group.html#asfdoc_sam0_nvm_examples (http://asf.atmel.com/docs/latest/samd21/html/group__asfdoc__sam0__nvm__group.html)

# FATFS

## FATFS API

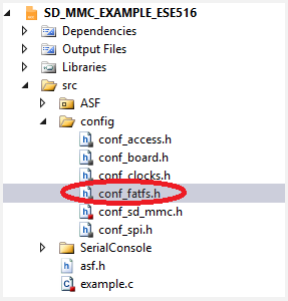
[picture p167: figure]

- Use the starter code for A6 to have a ready-to-go project with the SD Card and FatFS
- See “http://elm-chan.org/fsw/ff/00index_e.html ” for a list of the PAI present
- The example uses f_gets and f_puts which deal with text. If you want to read and write raw bytes, use f_read and f_write.
- Not all options are turned on by default – if you need an extra function, please check “conf_fatfs.h” to turn the option you need on.

# JUMPING TO MAIN APPLICATION

## RUNNING APPLICATION CODE

- On boot, the MCU will look to the 0x0000 address – this gives the stack pointer and reset handler for the bootloader
- To transition to the application code, we must point to the application code space – “rebase” the stack pointer & reset vector
- The code on the right handles this functionality
- USB MSC: Page 31-32 has some good references
- http://www.atmel.com/images/atmel-42352-sam-d21-xpro-usb-host-msc-bootloader_trainingmanual_an8185.pdf (http://www.atmel.com/images/atmel-42352-sam-d21-xpro-usb-host-msc-bootloader_training-manual_an8185.pdf)

#define APP_START_ADDRESS ((uint32_t)0x2000) //Must be address of start of main application

/// Main application reset vector address
#define APP_START_RESET_VEC_ADDRESS (APP_START_ADDRESS+(uint32_t)0x04)

/**************************************************************************//**
* function | jumpToApplication()
* @brief | Jumps to main application
* @details | Detailed Description
* @note | Add a note
* @param[in] | arg1 Input parameter description
* @param[out] | arg2 Output parameter description
* @return | Description of return value
******************************************************************************/ static void jumpToApplication(void)
{
/// Function pointer to application section
void (*applicationCodeEntry)(void);

/// Rebase stack pointer
__set_MSP(*(uint32_t *) APP_START_ADDRESS);

/// Rebase vector table
SCB->VTOR = ((uint32_t) APP_START_ADDRESS & SCB_VTOR_TBLOFF_Msk);

/// Set pointer to application section
applicationCodeEntry =
(void (*)(void))(unsigned *)(*(unsigned *)(APP_START_RESET_VEC_ADDRESS));

/// Jump to application
applicationCodeEntry();
}
