sheilsarda/IoT_Thermal_Camera/Lab7/A7 Submission/Q1_Node_Red/Node Red Topiccs diagram.pdf

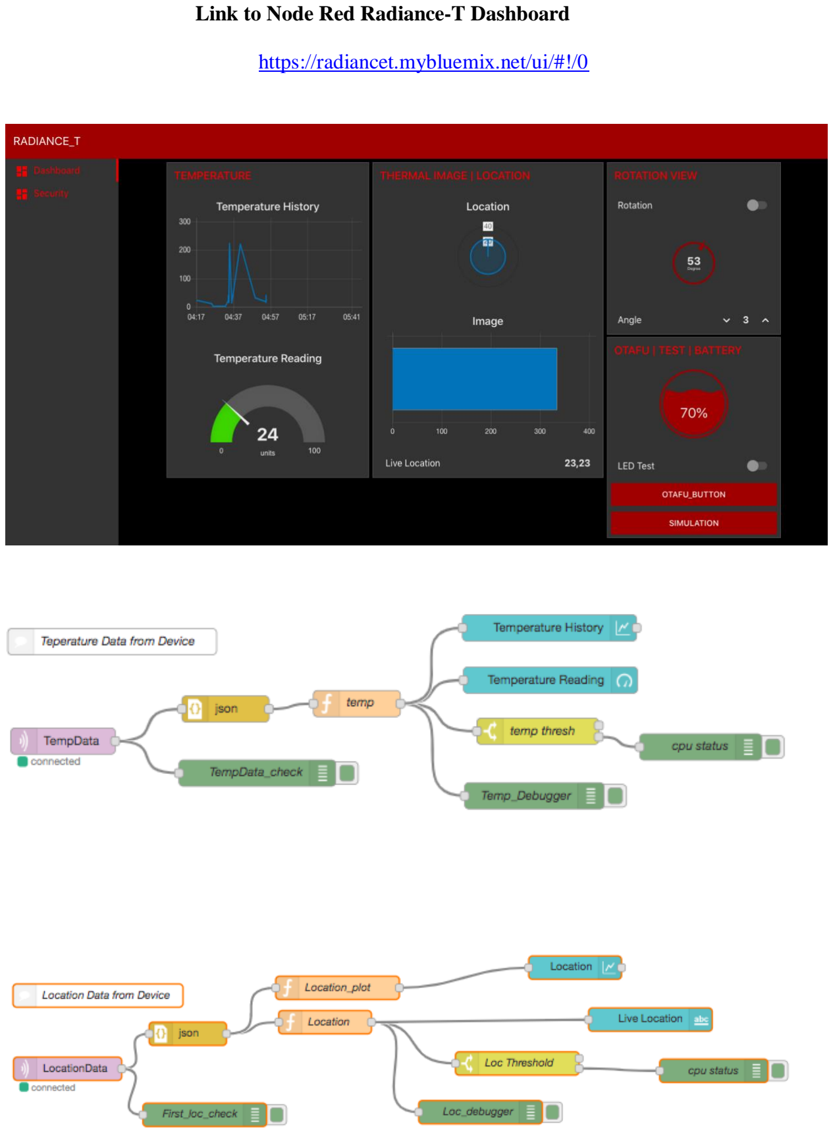
[picture p168: page 1]

Link to Node Red Radiance-T Dashboard

https://radiancet.mybluemix.net/ui/#!/0

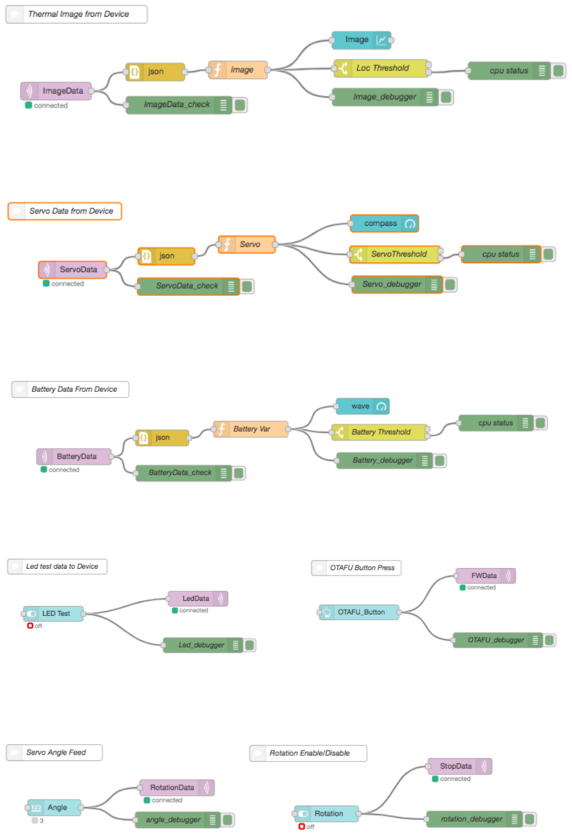
[picture p169: page 2]
