sheilsarda/IoT_Thermal_Camera/imgs/5V Boost Circuit.PNG

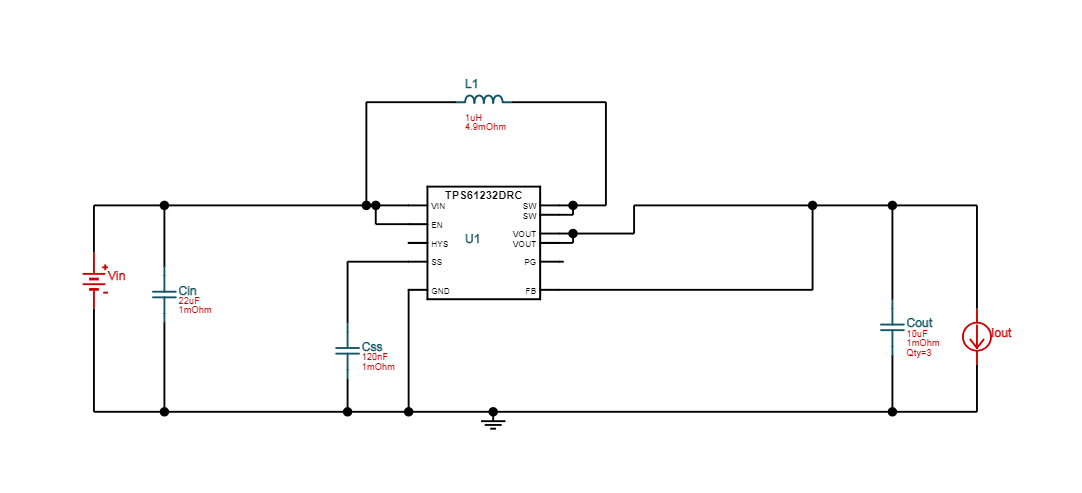
imgs/5V Boost Circuit.PNG
