sheilsarda/IoT_Thermal_Camera/Lab4/Nikhil Jamdade.png

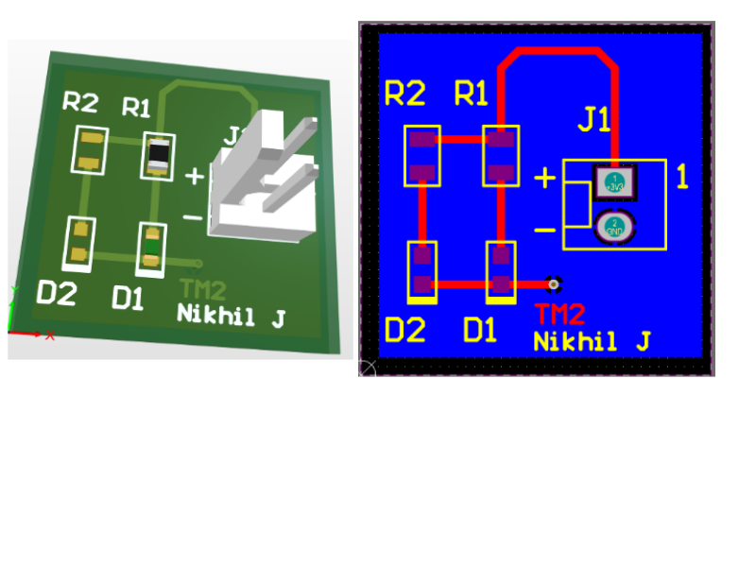
Lab4/Nikhil Jamdade.png
