sheilsarda/IoT_Thermal_Camera/Lab7/A7 Submission/Q1_Node_Red/MetaData Feed.png

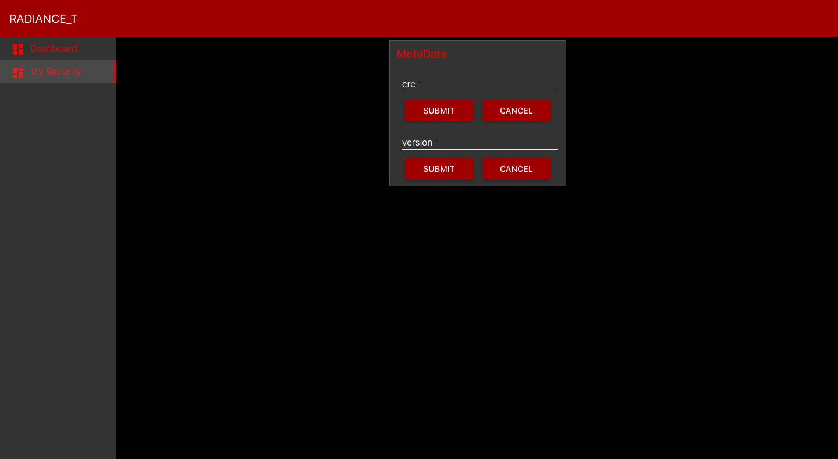
Lab7/A7 Submission/Q1_Node_Red/MetaData Feed.png
