sheilsarda/IoT_Thermal_Camera/Lab7/A7 Submission/Q2_OTAFU DEMO/Dashboard Topics.gif

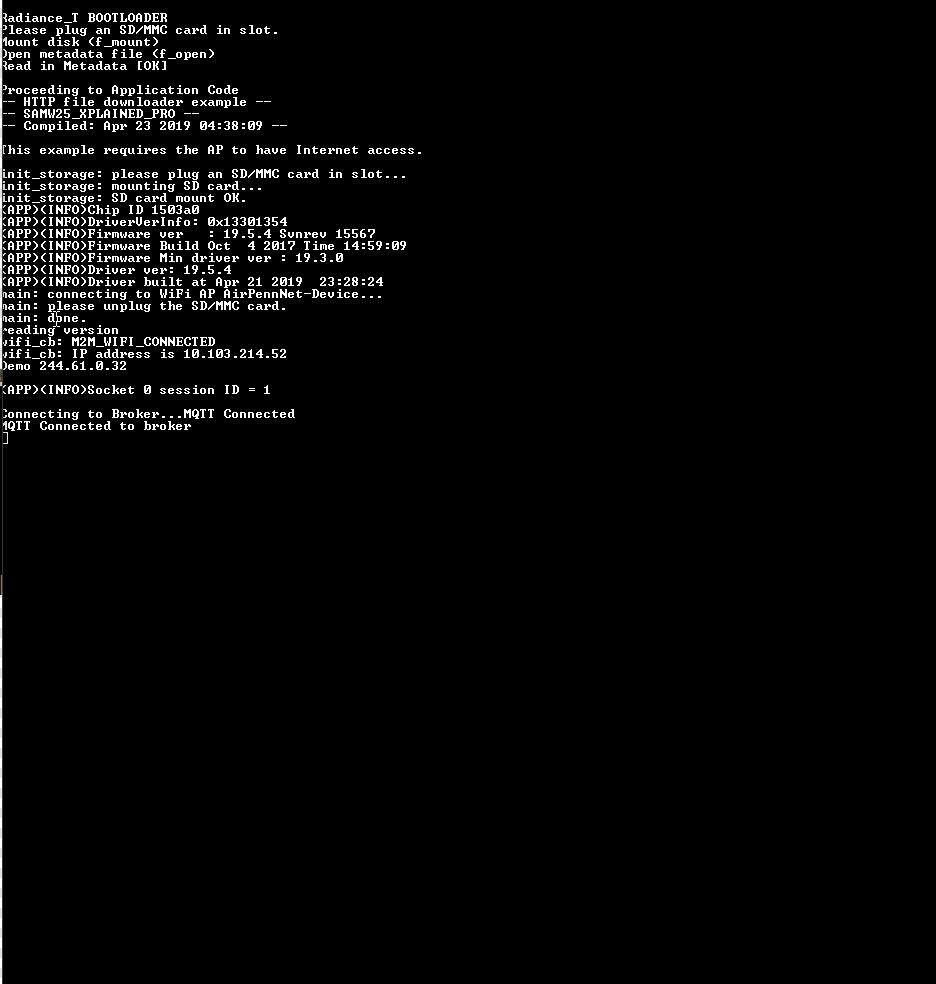
Lab7/A7 Submission/Q2_OTAFU DEMO/Dashboard Topics.gif
