sheilsarda/IoT_Thermal_Camera/Lab7/A7 Submission/Q3_Project Package/CLI after OTAFU.gif

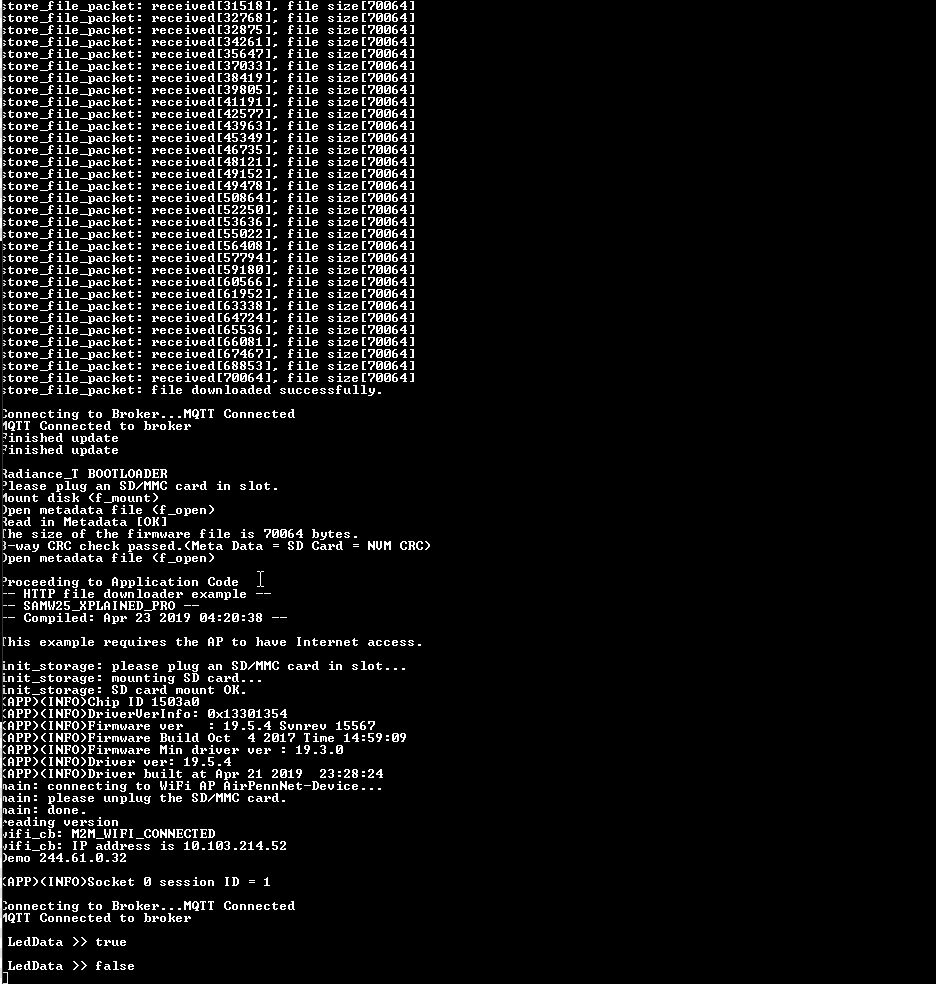
Lab7/A7 Submission/Q3_Project Package/CLI after OTAFU.gif
