sheilsarda/IoT_Thermal_Camera/Lab7/A7 Submission/Q3_Project Package/CLI before OTAFU.gif

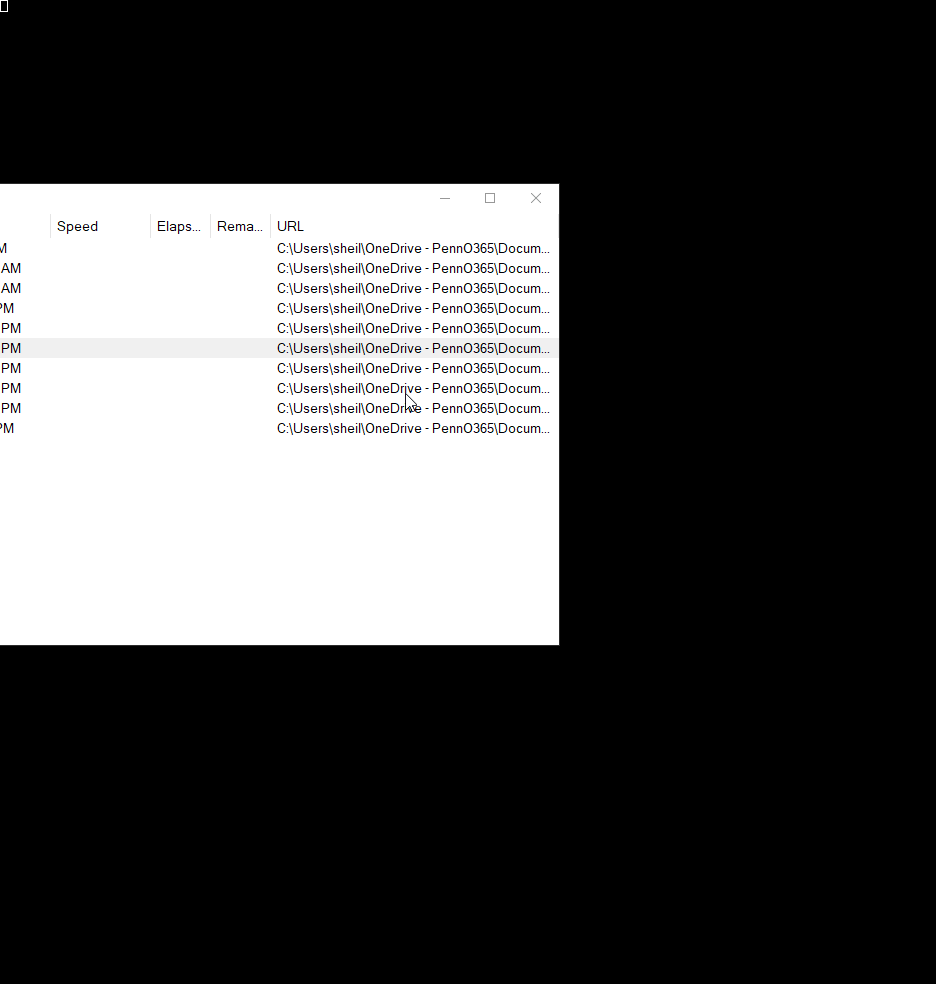
Lab7/A7 Submission/Q3_Project Package/CLI before OTAFU.gif
