sheilsarda/IoT_Thermal_Camera/Lab8/MQTT Dashboard Features.gif

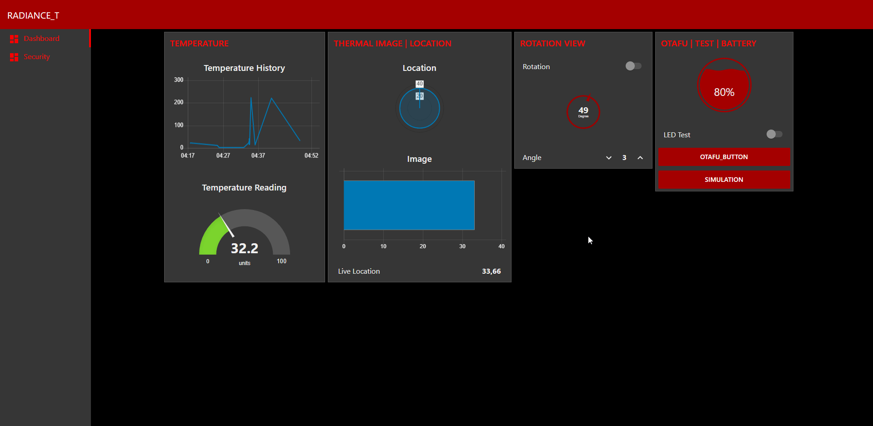
Lab8/MQTT Dashboard Features.gif
