sheilsarda/IoT_Thermal_Camera/Lab7/Radiance_V0/Radiance_V0/src/ASF/common/components/wifi/winc1500/driver/include/m2m_types.h

/**
 *
 * \file
 *
 * \brief WINC Application Interface Internal Types.
 *
 * Copyright (c) 2016-2018 Microchip Technology Inc. and its subsidiaries.
 *
 * \asf_license_start
 *
 * \page License
 *
 * Subject to your compliance with these terms, you may use Microchip
 * software and any derivatives exclusively with Microchip products.
 * It is your responsibility to comply with third party license terms applicable
 * to your use of third party software (including open source software) that
 * may accompany Microchip software.
 *
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
 * \asf_license_stop
 *
 */

#ifndef __M2M_WIFI_TYPES_H__
#define __M2M_WIFI_TYPES_H__


/*=*=*=*=*=*=*=*=*=*=*=*=*=*=*=*=*=*=*=*=*=*=*=*=*=*=*=*=*=*=*=*=*=*=*=*=*=*=*=*=*=*=*=*=*=*=*=*=*=*
INCLUDES
*=*=*=*=*=*=*=*=*=*=*=*=*=*=*=*=*=*=*=*=*=*=*=*=*=*=*=*=*=*=*=*=*=*=*=*=*=*=*=*=*=*=*=*=*=*=*=*=*=*/
#ifndef	_BOOT_
#ifndef _FIRMWARE_
#include "common/include/nm_common.h"
#else
#ifndef LINT
#include "m2m_common.h"
#else
#include "../../../firmware/wifi_v111/src/m2m/include/m2m_common.h"
#endif
#endif
#endif


/*=*=*=*=*=*=*=*=*=*=*=*=*=*=*=*=*=*=*=*=*=*=*=*=*=*=*=*=*=*=*=*=*=*=*=*=*=*=*=*=*=*=*=*=*=*=*=*=*=*
MACROS
*=*=*=*=*=*=*=*=*=*=*=*=*=*=*=*=*=*=*=*=*=*=*=*=*=*=*=*=*=*=*=*=*=*=*=*=*=*=*=*=*=*=*=*=*=*=*=*=*=*/
/**@defgroup  WlanDefines Defines
 * @ingroup m2m_wifi
 */
/**@{*/
#define M2M_MAJOR_SHIFT (8)
#define M2M_MINOR_SHIFT (4)
#define M2M_PATCH_SHIFT (0)

#define M2M_DRV_VERSION_SHIFT (16)
#define M2M_FW_VERSION_SHIFT (0)

#define M2M_GET_MAJOR(ver_info_hword) ((uint8)((ver_info_hword) >> M2M_MAJOR_SHIFT) & 0xff)
#define M2M_GET_MINOR(ver_info_hword) ((uint8)((ver_info_hword) >> M2M_MINOR_SHIFT) & 0x0f)
#define M2M_GET_PATCH(ver_info_hword) ((uint8)((ver_info_hword) >> M2M_PATCH_SHIFT) & 0x0f)

#define M2M_GET_FW_VER(ver_info_word)  ((uint16) ((ver_info_word) >> M2M_FW_VERSION_SHIFT))
#define M2M_GET_DRV_VER(ver_info_word) ((uint16) ((ver_info_word) >> M2M_DRV_VERSION_SHIFT))

#define M2M_GET_DRV_MAJOR(ver_info_word) M2M_GET_MAJOR(M2M_GET_DRV_VER(ver_info_word))
#define M2M_GET_DRV_MINOR(ver_info_word) M2M_GET_MINOR(M2M_GET_DRV_VER(ver_info_word))
#define M2M_GET_DRV_PATCH(ver_info_word) M2M_GET_PATCH(M2M_GET_DRV_VER(ver_info_word))

#define M2M_GET_FW_MAJOR(ver_info_word) M2M_GET_MAJOR(M2M_GET_FW_VER(ver_info_word))
#define M2M_GET_FW_MINOR(ver_info_word) M2M_GET_MINOR(M2M_GET_FW_VER(ver_info_word))
#define M2M_GET_FW_PATCH(ver_info_word) M2M_GET_PATCH(M2M_GET_FW_VER(ver_info_word))

#define M2M_MAKE_VERSION(major, minor, patch) ( \
	((uint16)((major)  & 0xff)  << M2M_MAJOR_SHIFT) | \
	((uint16)((minor)  & 0x0f)  << M2M_MINOR_SHIFT) | \
	((uint16)((patch)  & 0x0f)  << M2M_PATCH_SHIFT))

#define M2M_MAKE_VERSION_INFO(fw_major, fw_minor, fw_patch, drv_major, drv_minor, drv_patch) \
	( \
	( ((uint32)M2M_MAKE_VERSION((fw_major),  (fw_minor),  (fw_patch)))  << M2M_FW_VERSION_SHIFT) | \
	( ((uint32)M2M_MAKE_VERSION((drv_major), (drv_minor), (drv_patch))) << M2M_DRV_VERSION_SHIFT))

#define REL_19_5_3_VER			M2M_MAKE_VERSION_INFO(19,5,3,19,3,0)
#define REL_19_5_2_VER			M2M_MAKE_VERSION_INFO(19,5,2,19,3,0)
#define REL_19_5_1_VER			M2M_MAKE_VERSION_INFO(19,5,1,19,3,0)
#define REL_19_5_0_VER			M2M_MAKE_VERSION_INFO(19,5,0,19,3,0)
#define REL_19_4_6_VER			M2M_MAKE_VERSION_INFO(19,4,6,19,3,0)
#define REL_19_4_5_VER			M2M_MAKE_VERSION_INFO(19,4,5,19,3,0)
#define REL_19_4_4_VER			M2M_MAKE_VERSION_INFO(19,4,4,19,3,0)
#define REL_19_4_3_VER			M2M_MAKE_VERSION_INFO(19,4,3,19,3,0)
#define REL_19_4_2_VER			M2M_MAKE_VERSION_INFO(19,4,2,19,3,0)
#define REL_19_4_1_VER			M2M_MAKE_VERSION_INFO(19,4,1,19,3,0)
#define REL_19_4_0_VER			M2M_MAKE_VERSION_INFO(19,4,0,19,3,0)
#define REL_19_3_1_VER			M2M_MAKE_VERSION_INFO(19,3,1,19,3,0)
#define REL_19_3_0_VER			M2M_MAKE_VERSION_INFO(19,3,0,19,3,0)
#define REL_19_2_2_VER			M2M_MAKE_VERSION_INFO(19,2,2,19,2,0)
#define REL_19_2_1_VER			M2M_MAKE_VERSION_INFO(19,2,1,19,2,0)
#define REL_19_2_0_VER			M2M_MAKE_VERSION_INFO(19,2,0,19,2,0)
#define REL_19_1_0_VER			M2M_MAKE_VERSION_INFO(19,1,0,18,2,0)
#define REL_19_0_0_VER			M2M_MAKE_VERSION_INFO(19,0,0,18,1,1)

/*======*======*======*======*
		FIRMWARE VERSION NO INFO
 *======*======*======*======*/

#define M2M_RELEASE_VERSION_MAJOR_NO 						(19)
/*!< Firmware Major release version number.
*/


#define M2M_RELEASE_VERSION_MINOR_NO						(5)
/*!< Firmware Minor release version number.
*/

#define M2M_RELEASE_VERSION_PATCH_NO						(4)
/*!< Firmware patch release version number.
*/
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
